vincentkslim/Ender-3/Ender-3 Mechanical/Ender-3 Parts/ASM Roller Z-Axis Left.SLDASM

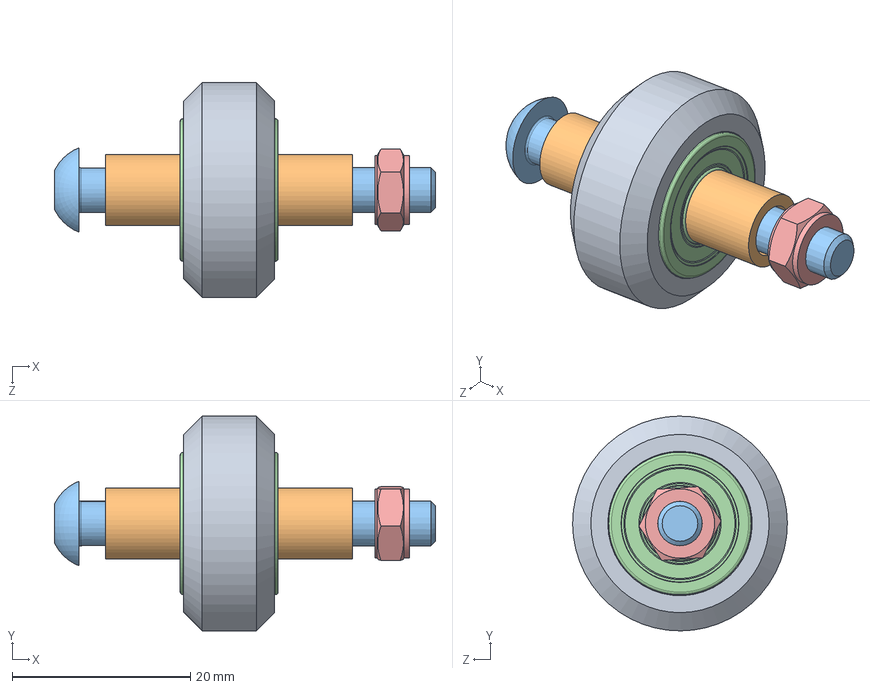
[picture p16: CAD file, 2020-07-11]
Ender-3 Mechanical/Ender-3 Parts/ASM Roller Z-Axis Left.SLDASM
42.8 x 24.1 x 24.1 mm
Rollers
Spacers for rollers x 2
M5X40 Pan Head Screw
625pillow x 2
M5 Self-locking nut
