vincentkslim/Ender-3/Ender-3 Mechanical/Ender-3 Parts/ASM Bed.SLDASM

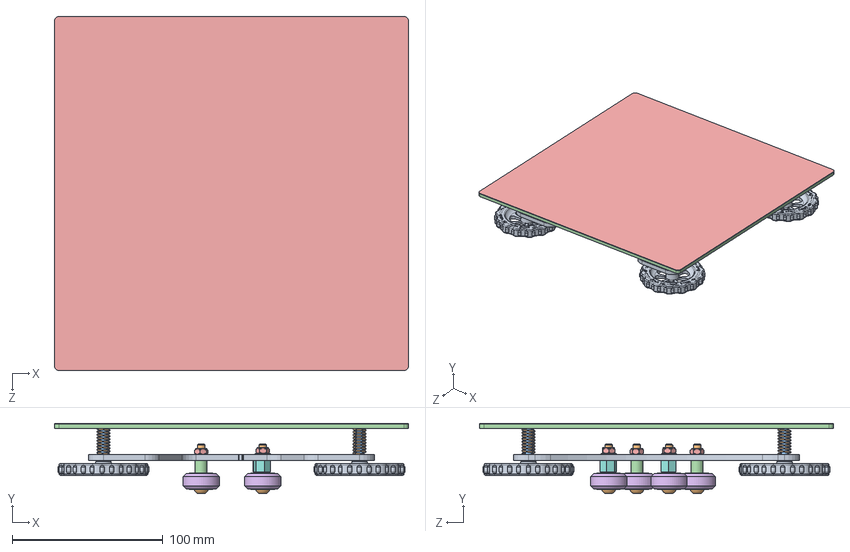
[picture p17: CAD file, 2020-07-11]
Ender-3 Mechanical/Ender-3 Parts/ASM Bed.SLDASM
235.0 x 46.7 x 235.0 mm
Y plate
M5X30 Pan Head Screw x 4
625pillow x 8
Spacers for rollers x 2
M5 Self-locking nut x 4
Rollers x 4
M5 washer x 2
Eccentric column x 2
Hand Twisted Nut x 4
Bed level springs x 4
M4X30 Flush Head Screw x 4
Hot bed
Hotbed_Surface
