vincentkslim/Ender-3/Ender-3 Mechanical/Ender-3 Parts/ASM Eccentrical Roller Z-Axis Right.SLDASM

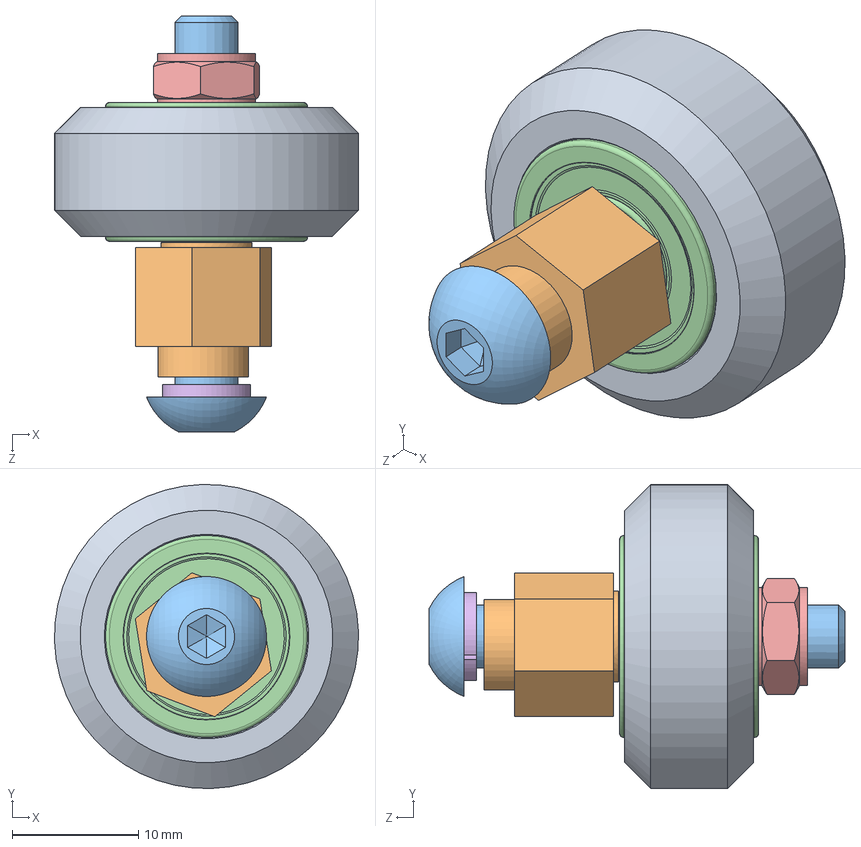
[picture p18: CAD file, 2020-07-11]
Ender-3 Mechanical/Ender-3 Parts/ASM Eccentrical Roller Z-Axis Right.SLDASM
24.1 x 24.1 x 33.0 mm
Rollers
Eccentric column
M5X30 Pan Head Screw
625pillow x 2
M5 Self-locking nut
M5 Split Washer
