vincentkslim/Ender-3/Ender-3 Mechanical/Ender-3 Parts/ASM Display.SLDASM

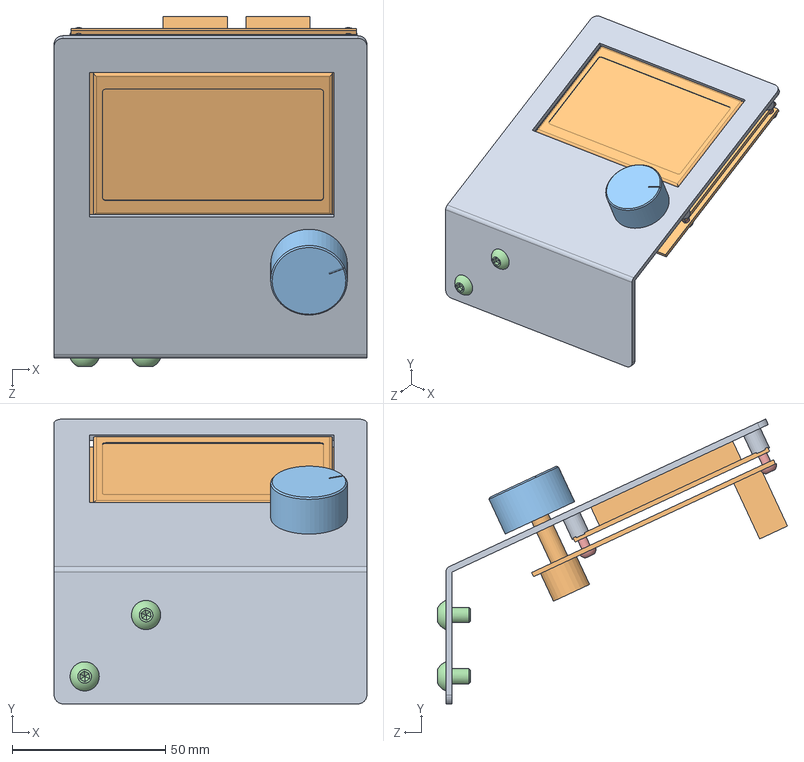
[picture p19: CAD file, 2020-04-29]
Ender-3 Mechanical/Ender-3 Parts/ASM Display.SLDASM
102.0 x 92.9 x 114.1 mm
LCD support
lcd
lcd Knob
M5X8Pan Head Screw x 2
M3X8 Pan Head Screw x 4
