vincentkslim/Ender-3/Ender-3 Mechanical/Ender-3 Parts/ASM Electronic Enclosure.SLDASM

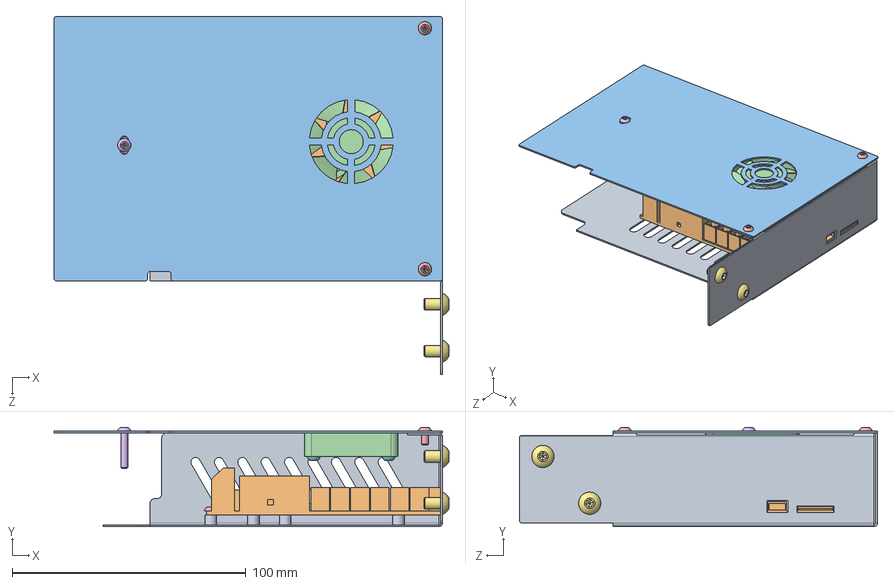
[picture p20: CAD file, 2020-04-29]
Ender-3 Mechanical/Ender-3 Parts/ASM Electronic Enclosure.SLDASM
168.8 x 42.5 x 153.0 mm
Sheetmetal enclosure bottom
Control panel
Sheetmetal enclosure top
Case fan
M3X6Pan Head Screw x 6
M3X16 Pan Head Screw
M5X8Pan Head Screw x 2
M3X10 Pan Head Screw x 2
