vincentkslim/Ender-3/Ender-3 Mechanical/Ender-3 Parts/ASM Y-Axis Limit Switch.SLDASM

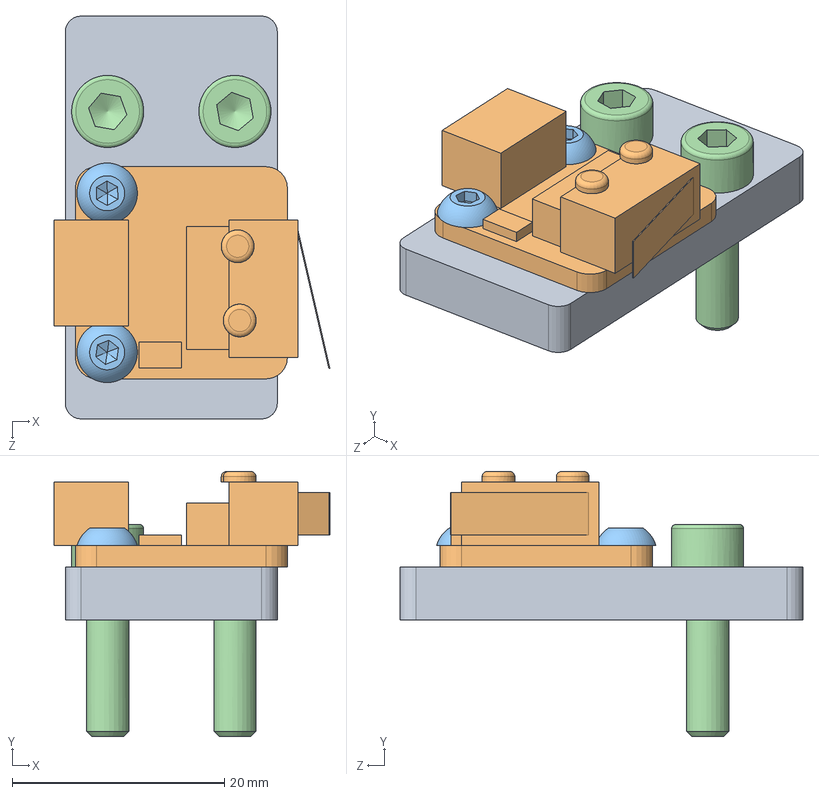
[picture p21: CAD file, 2020-04-29]
Ender-3 Mechanical/Ender-3 Parts/ASM Y-Axis Limit Switch.SLDASM
26.0 x 25.0 x 38.0 mm
Y limit switch bracket
limit switch
M3X6Pan Head Screw x 2
M4X16 Screw x 2
