vincentkslim/Ender-3/Ender-3 Mechanical/Ender-3 Parts/ASM Spool Holder.SLDASM

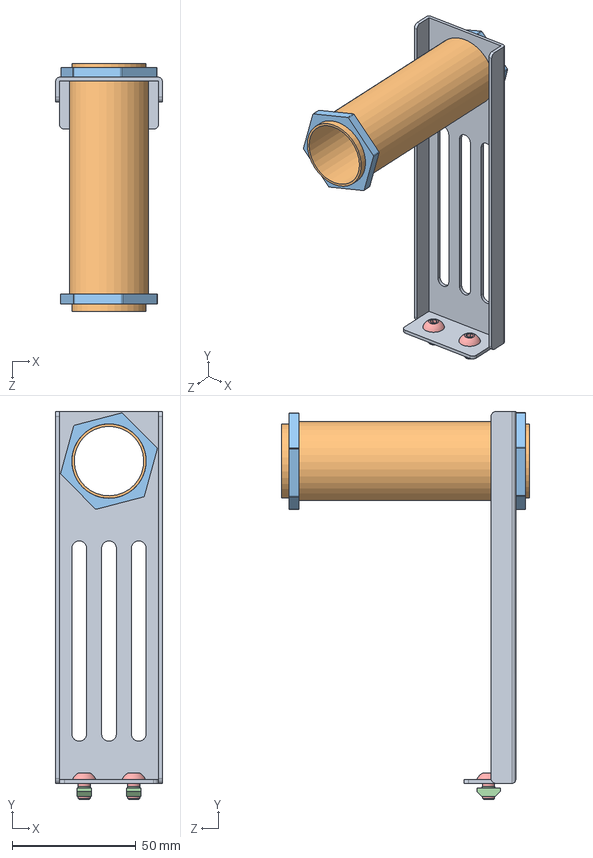
[picture p22: CAD file, 2020-04-29]
Ender-3 Mechanical/Ender-3 Parts/ASM Spool Holder.SLDASM
43.0 x 156.5 x 100.0 mm
Support frame
Support tube
M30 Plastic nut x 2
M4 T-Slot Nut x 2
M5X8Pan Head Screw x 2
