vincentkslim/Ender-3/Ender-3 Mechanical/Ender-3 Parts/ASM Y-Belt Tensioner.SLDASM

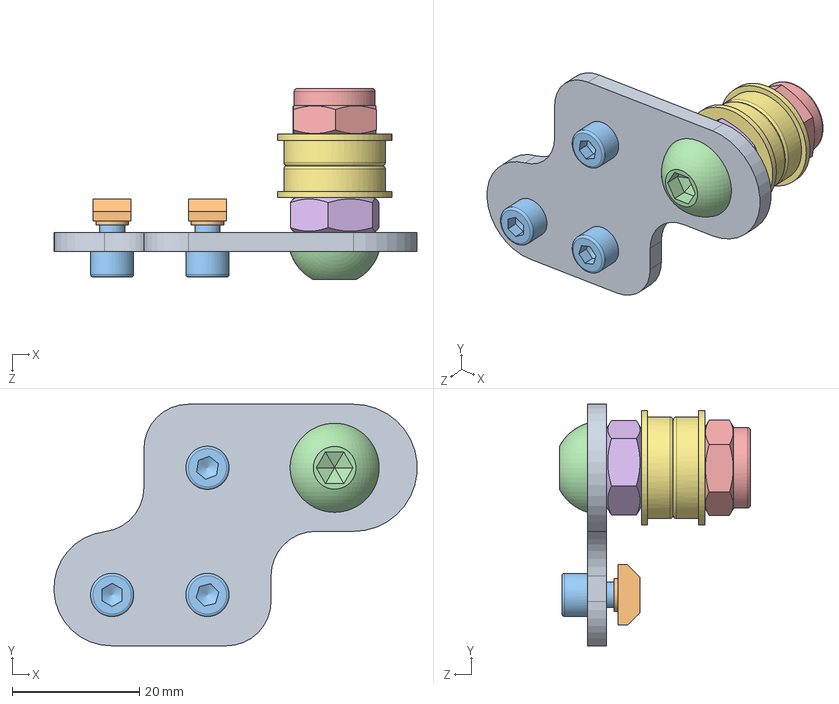
[picture p23: CAD file, 2020-04-29]
Ender-3 Mechanical/Ender-3 Parts/ASM Y-Belt Tensioner.SLDASM
57.1 x 38.0 x 30.1 mm
Y Adjustment Block
M4 T-Slot Nut x 3
M4X8 Socket Head Screw x 3
M8X25 Pan Head Screw
M8 Self-locking nut
M8 nut
F688 pillow x 2
