vincentkslim/Ender-3/Ender-3 Mechanical/Ender-3 Parts/ASM Z-Axis Limit Switch.SLDASM

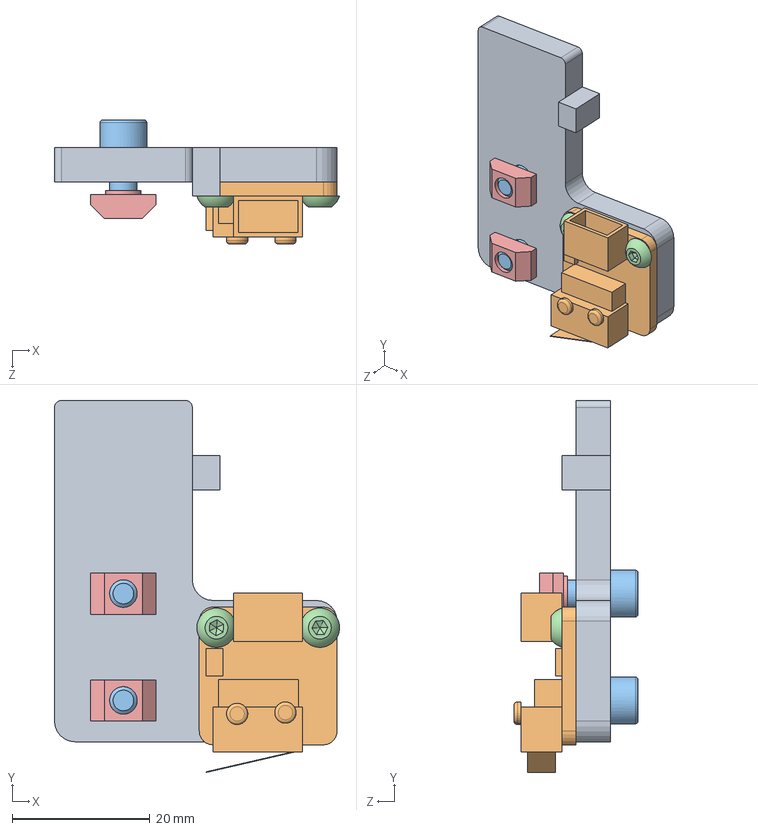
[picture p24: CAD file, 2020-04-29]
Ender-3 Mechanical/Ender-3 Parts/ASM Z-Axis Limit Switch.SLDASM
41.3 x 54.0 x 18.0 mm
Z limit switch bracket
limit switch
M4X10 Socket Head Screw x 2
M3X6Pan Head Screw x 2
M4 T-Slot Nut x 2
