vincentkslim/Ender-3/Ender-3 Mechanical/Ender-3 Parts/ASM Power Supply.SLDASM

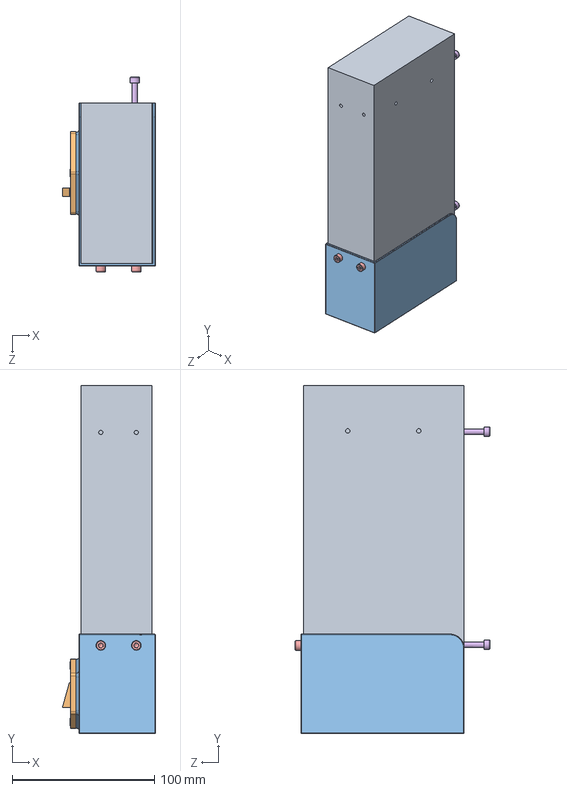
[picture p25: CAD file, 2020-04-29]
Ender-3 Mechanical/Ender-3 Parts/ASM Power Supply.SLDASM
65.5 x 245.0 x 137.0 mm
24V15A power supply
power switch
Power holder
M3X10 Flush Head Screw x 2
M4X8 Socket Head Screw x 2
M4X20 Socket Head Screw x 2
