vincentkslim/Ender-3/Ender-3 Mechanical/Ender-3 Parts/ASM Z-Axis.SLDASM

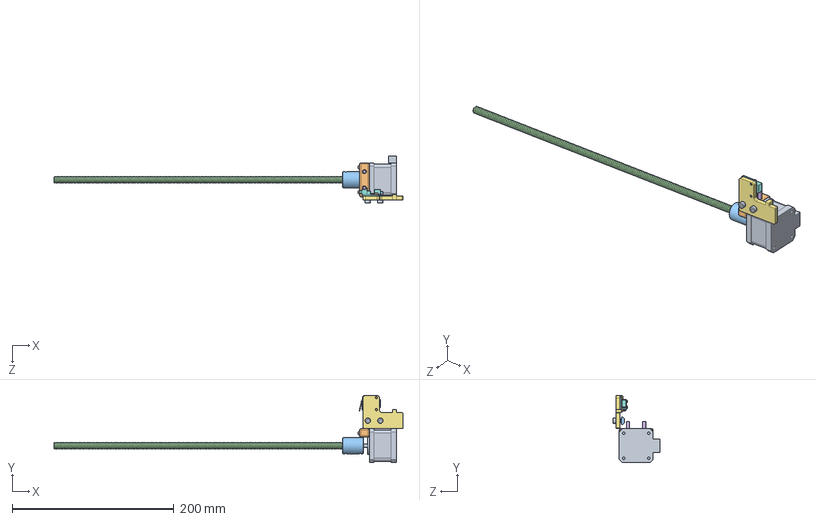
[picture p26: CAD file, 2020-04-29]
Ender-3 Mechanical/Ender-3 Parts/ASM Z-Axis.SLDASM
431.8 x 83.3 x 58.7 mm
42-34 motor
Z motor bracket
Z coupler
Z threaded rod
M3X16 Pan Head Screw x 2
M4X18 Flush Head Screw x 2
Z limit switch bracket
limit switch
M4X10 Socket Head Screw x 2
M3X6Pan Head Screw x 2
M4 T-Slot Nut x 2
