vincentkslim/Ender-3/Ender-3 Mechanical/Ender-3 Parts/ASM Frame.SLDASM

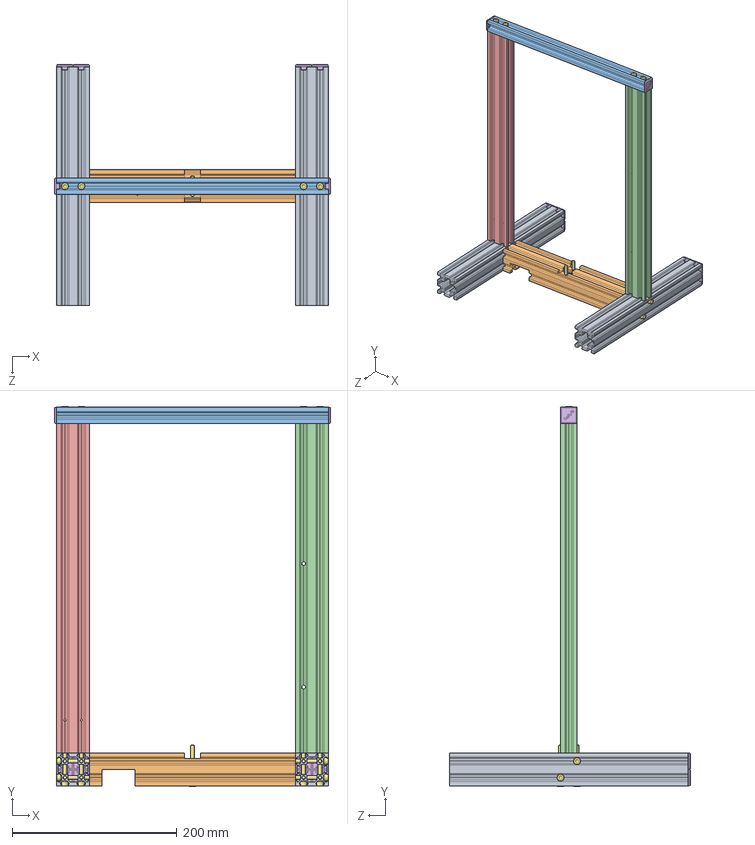
[picture p27: CAD file, 2020-04-09]
Ender-3 Mechanical/Ender-3 Parts/ASM Frame.SLDASM
335.7 x 461.6 x 292.9 mm
4040 profile x 2
4040-3 profile
2020-2 profile
2040-3R profile
2040-3L profile
2020 Endcap x 10
M5X45 Socket Head Screw x 14
