vincentkslim/Ender-3/Ender-3 Mechanical/Ender-3 Parts/ASM Y-Axis.SLDASM

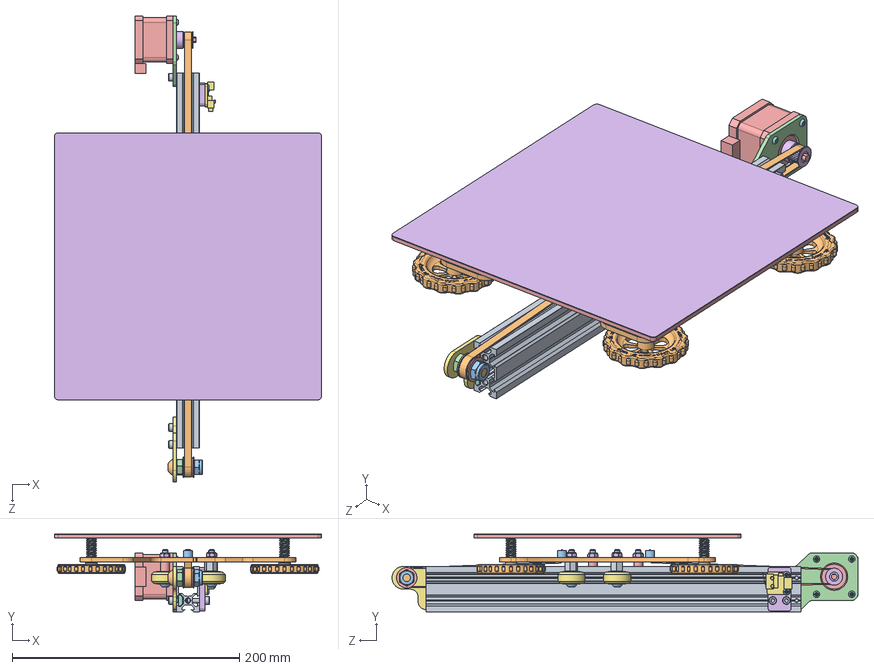
[picture p28: CAD file, 2020-04-09]
Ender-3 Mechanical/Ender-3 Parts/ASM Y-Axis.SLDASM
235.0 x 68.5 x 410.1 mm
2040-2 profile
Y belt
Copper cover x 2
Y Motor holder
42-34 motor
2GT-pulley
Y Adjustment Block
M4 T-Slot Nut x 3
M4X8 Socket Head Screw x 3
M8X25 Pan Head Screw
M8 Self-locking nut
M8 nut
F688 pillow x 2
Y limit switch bracket
limit switch
M3X6Pan Head Screw x 6
M4X16 Screw x 4
Y plate
M5X30 Pan Head Screw x 4
625pillow x 8
Spacers for rollers x 2
M5 Self-locking nut x 4
Rollers x 4
M5 washer x 2
Eccentric column x 2
Hand Twisted Nut x 4
Bed level springs x 4
M4X30 Flush Head Screw x 4
Hot bed
Hotbed_Surface
