vincentkslim/Ender-3/Ender-3 Mechanical/Ender-3 Upgrades/raspberry-pi-3-model-b-reference-design-solidworks-cad-rpi-raspberrypi-raspberry-pi-1.snapshot.83/Solidworks Complete Assembly/Rpi components/RPi3_ModelB v1.sldasm

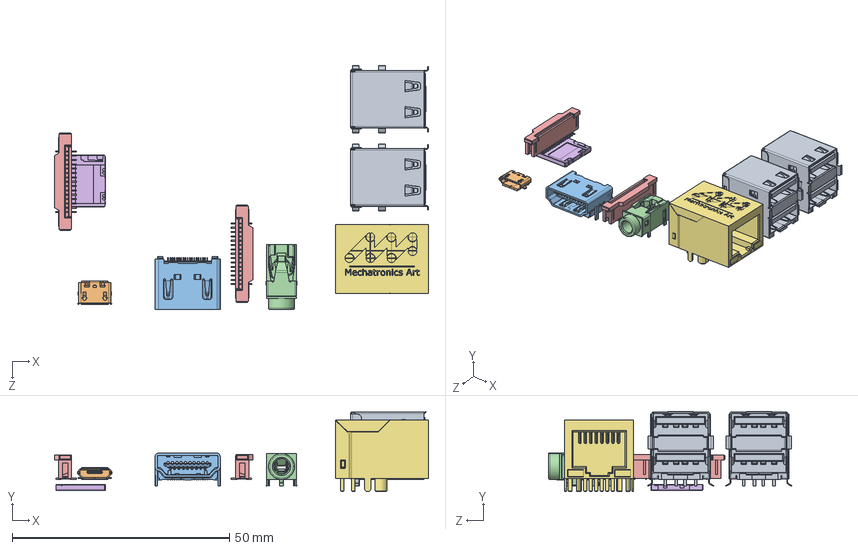
[picture p29: CAD file, 2020-04-29]
Ender-3 Mechanical/Ender-3 Upgrades/raspberry-pi-3-model-b-reference-design-solidworks-cad-rpi-raspberrypi-raspberry-pi-1.snapshot.83/Solidworks Complete Assembly/Rpi components/RPi3_ModelB v1.sldasm
86.1 x 18.5 x 56.1 mm
MOLEX_672983090 x 2
molex_0473460001
molex_0471510001
PJ-322
te_1-1734248-5 x 2
MOLEX_1040310811
raspberry_pi_B_(RJ45)
