vincentkslim/Ender-3/Ender-3 Mechanical/Ender-3 Upgrades/ABL/4mm allen key.SLDPRT

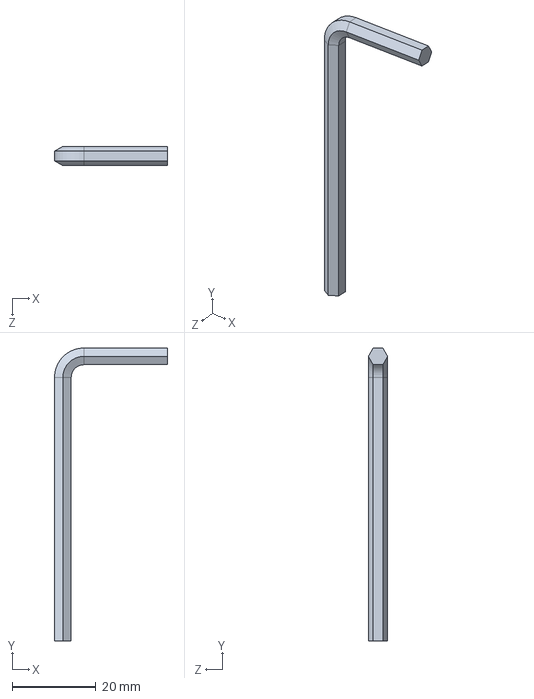
[picture p30: CAD file, 2020-04-29]
Ender-3 Mechanical/Ender-3 Upgrades/ABL/4mm allen key.SLDPRT
27.0 x 70.0 x 4.62 mm
