vincentkslim/Ender-3/Ender-3 Mechanical/Ender-3 Upgrades/Direct Drive/_stl/direct_drive_fits_e3d_v6_hero_me.STL

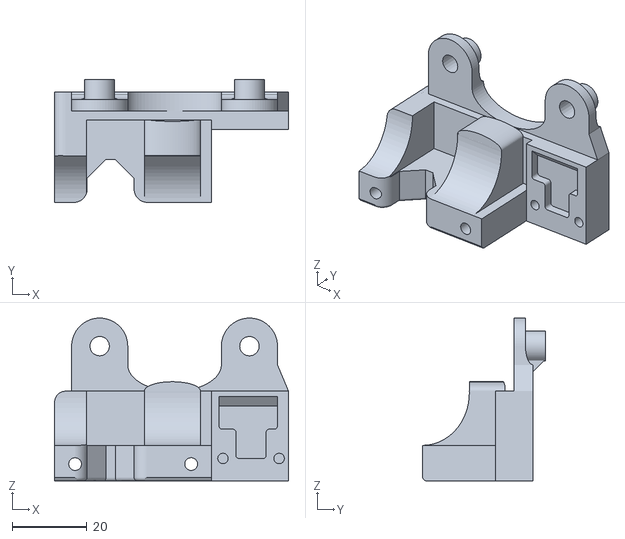
[picture p31: CAD file, 2020-04-29]
Ender-3 Mechanical/Ender-3 Upgrades/Direct Drive/_stl/direct_drive_fits_e3d_v6_hero_me.STL
62.5 x 32.8 x 43.5
