vincentkslim/Ender-3/Ender-3 Mechanical/Ender-3 Upgrades/Direct Drive/_test/part2.sldprt

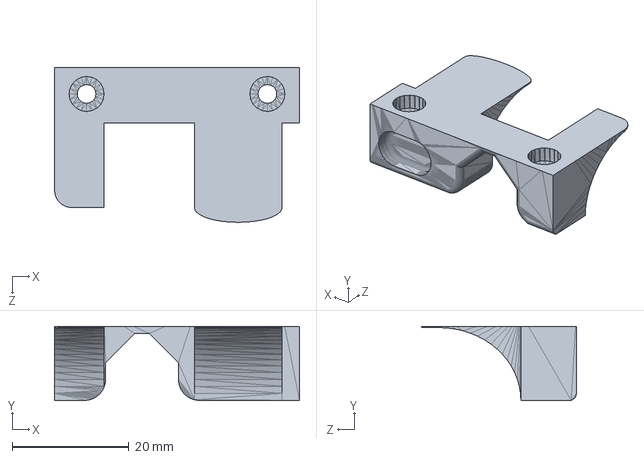
[picture p32: CAD file, 2020-04-29]
Ender-3 Mechanical/Ender-3 Upgrades/Direct Drive/_test/part2.sldprt
42.0 x 12.7 x 26.5 mm
