vincentkslim/Ender-3/Ender-3 Mechanical/Ender-3 Upgrades/Hero Me E3D V6 Mount/_stl/Hero_Me_E3D_Base_2_Gen2.stl

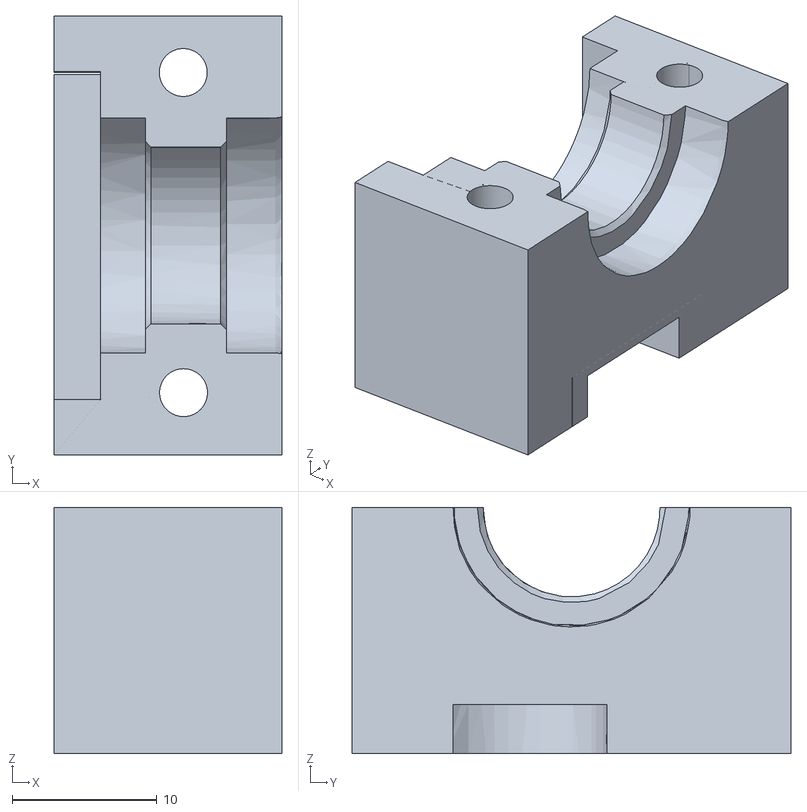
[picture p33: CAD file, 2020-04-29]
Ender-3 Mechanical/Ender-3 Upgrades/Hero Me E3D V6 Mount/_stl/Hero_Me_E3D_Base_2_Gen2.stl
15.7 x 30.3 x 17.0
