vincentkslim/Ender-3/Ender-3 Mechanical/Ender-3 Upgrades/Hero Me E3D V6 Mount/_test/1.5mm allen key test 2.2.STL

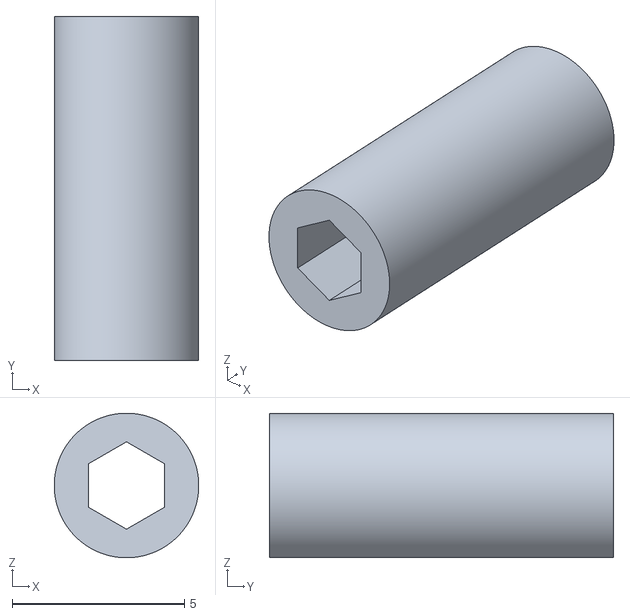
[picture p34: CAD file, 2020-04-29]
Ender-3 Mechanical/Ender-3 Upgrades/Hero Me E3D V6 Mount/_test/1.5mm allen key test 2.2.STL
4.20 x 10.0 x 4.20
