vincentkslim/Ender-3/Ender-3 Mechanical/Ender-3 Upgrades/Hero Me E3D V6 Mount/Hero_Me_Base_Lock_Gen3.SLDPRT

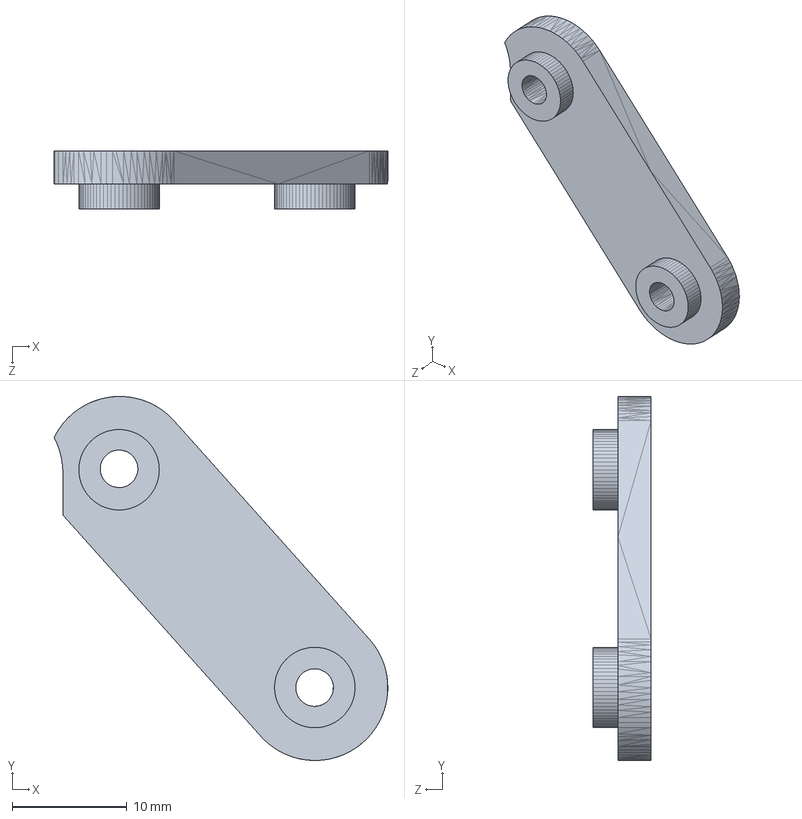
[picture p35: CAD file, 2020-04-29]
Ender-3 Mechanical/Ender-3 Upgrades/Hero Me E3D V6 Mount/Hero_Me_Base_Lock_Gen3.SLDPRT
29.0 x 31.7 x 5.07 mm
