vincentkslim/Ender-3/Ender-3 Mechanical/Ender-3 Upgrades/Radial Cooling Fan 50mm DC12V/Radial-Cooling-Fan-5015-DC12V.STEP

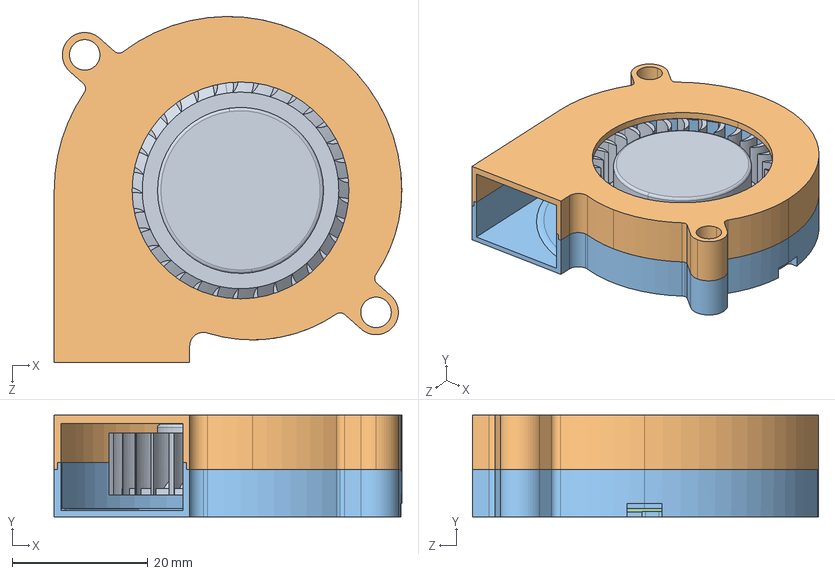
[picture p36: CAD file, 2020-07-11]
Ender-3 Mechanical/Ender-3 Upgrades/Radial Cooling Fan 50mm DC12V/Radial-Cooling-Fan-5015-DC12V.STEP
51.3 x 15.0 x 51.1 mm
turbine
top
bottom
