vincentkslim/Ender-3/Ender-3 Mechanical/Ender-3 Upgrades/Rear Electronics Case/_stl/fan_grill_3mm.STL

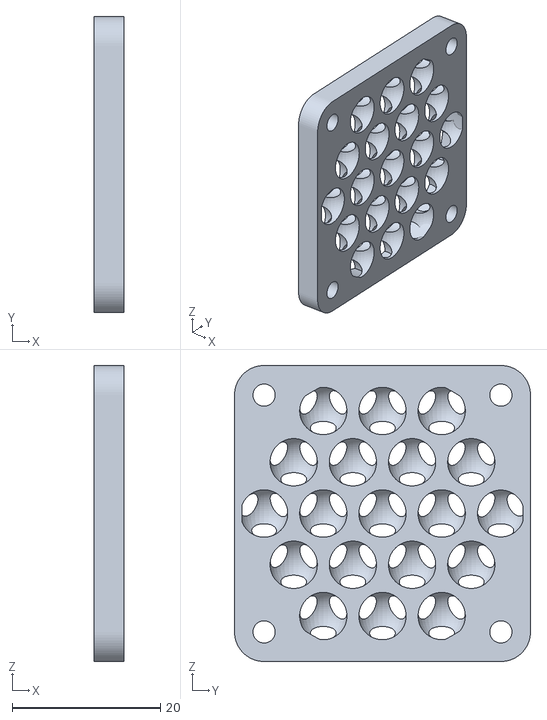
[picture p37: CAD file, 2020-04-29]
Ender-3 Mechanical/Ender-3 Upgrades/Rear Electronics Case/_stl/fan_grill_3mm.STL
4.00 x 40.0 x 40.0
