vincentkslim/Ender-3/Ender-3 Mechanical/Ender-3 Upgrades/Rear Electronics Case/case_right.SLDPRT

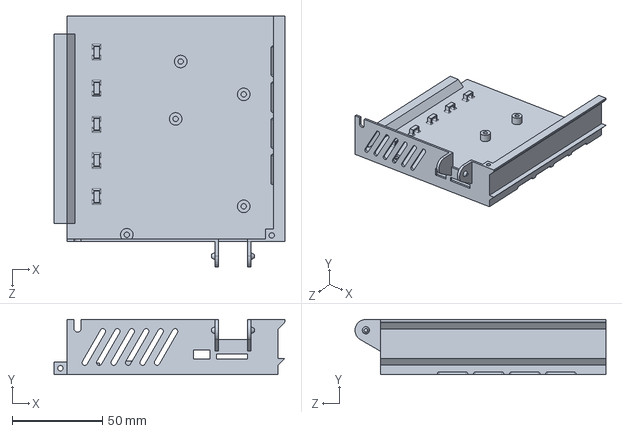
[picture p38: CAD file, 2020-12-05]
Ender-3 Mechanical/Ender-3 Upgrades/Rear Electronics Case/case_right.SLDPRT
127.8 x 30.5 x 139.0 mm
