vincentkslim/Ender-3/Ender-3 Mechanical/Ender-3 Upgrades/Samla Box clips/001.SLDPRT

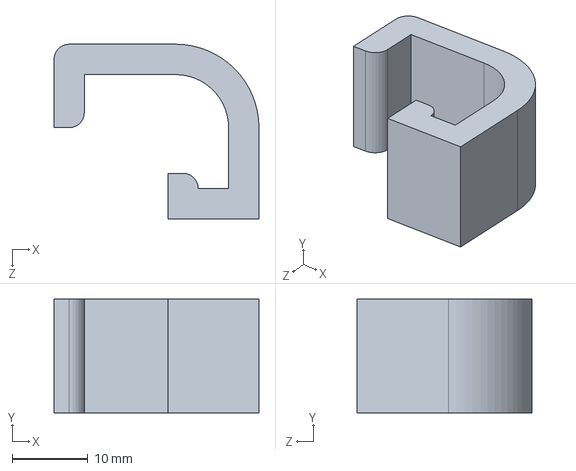
[picture p39: CAD file, 2020-12-05]
Ender-3 Mechanical/Ender-3 Upgrades/Samla Box clips/001.SLDPRT
27.0 x 15.0 x 23.0 mm
