vincentkslim/Ender-3/Ender-3 Mechanical/Ender-3 Upgrades/X Carriage/M6 thread test.SLDPRT

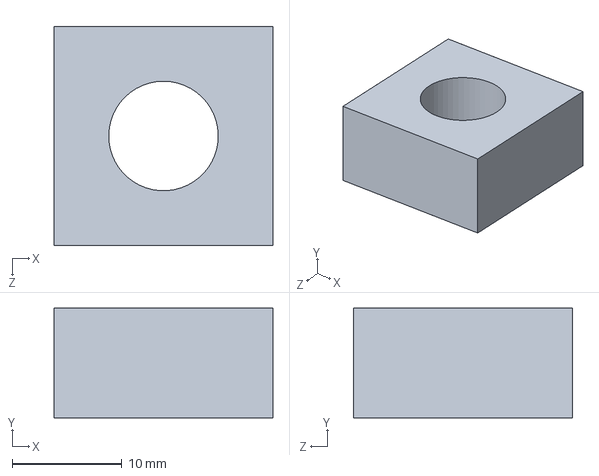
[picture p40: CAD file, 2020-12-05]
Ender-3 Mechanical/Ender-3 Upgrades/X Carriage/M6 thread test.SLDPRT
20.0 x 10.0 x 20.0 mm
