vincentkslim/Ender-3/Ender-3 Mechanical/Ender-3 Upgrades/ABL/1.5mm allen key.SLDPRT

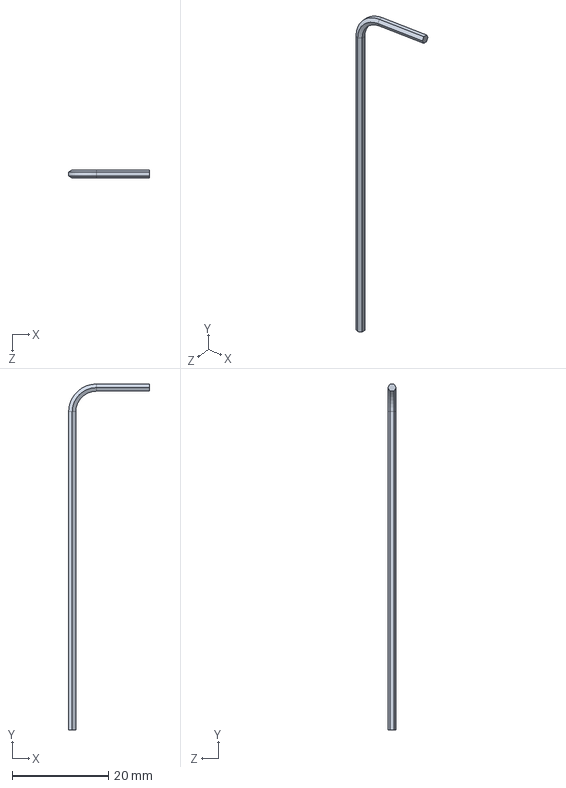
[picture p41: CAD file, 2020-04-29]
Ender-3 Mechanical/Ender-3 Upgrades/ABL/1.5mm allen key.SLDPRT
16.8 x 71.8 x 1.73 mm
