vincentkslim/Ender-3/Ender-3 Mechanical/Ender-3 Upgrades/Direct Drive/_test/Adapter_for_Red_Metal_Extruder_E3D_V6.STL

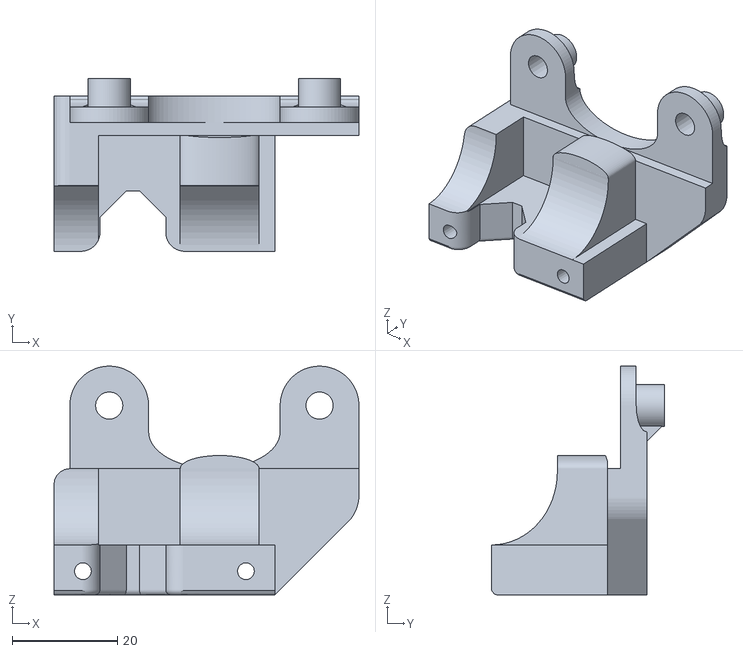
[picture p42: CAD file, 2020-04-29]
Ender-3 Mechanical/Ender-3 Upgrades/Direct Drive/_test/Adapter_for_Red_Metal_Extruder_E3D_V6.STL
58.0 x 32.8 x 43.5
