vincentkslim/Ender-3/Ender-3 Mechanical/Ender-3 Upgrades/Direct Drive/_test/fits_hero_me/Body3.sldprt

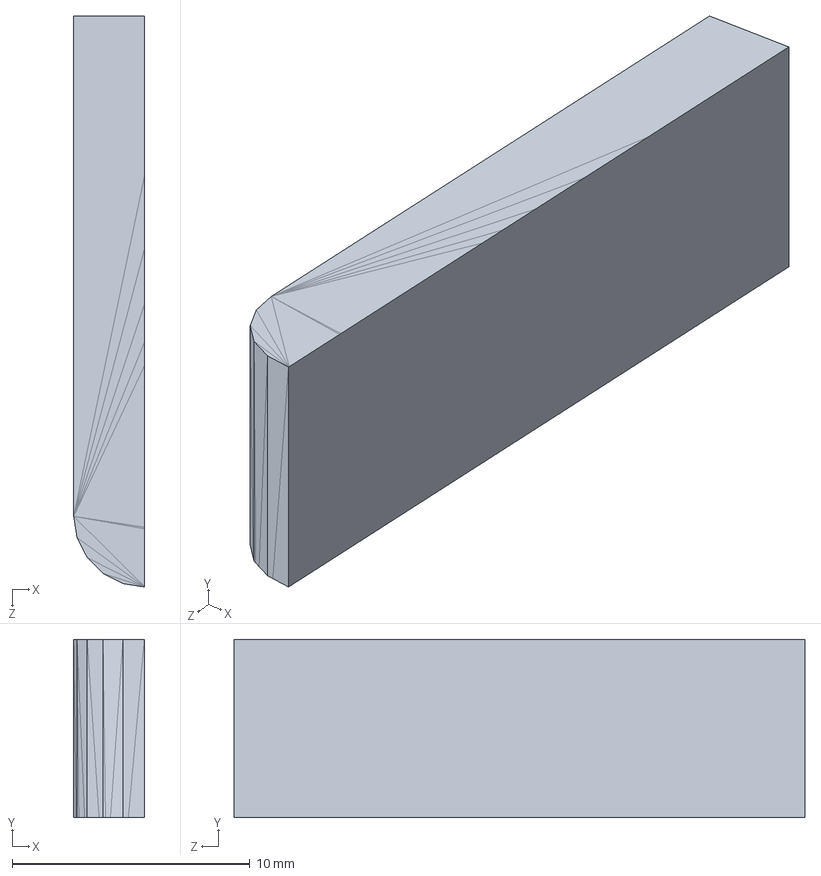
[picture p43: CAD file, 2020-04-29]
Ender-3 Mechanical/Ender-3 Upgrades/Direct Drive/_test/fits_hero_me/Body3.sldprt
2.97 x 7.50 x 24.0 mm
