vincentkslim/Ender-3/Ender-3 Mechanical/Ender-3 Upgrades/Hero Me E3D V6 Mount/_stl/Hero_Me_E3D_Base_1_Gen2c.stl

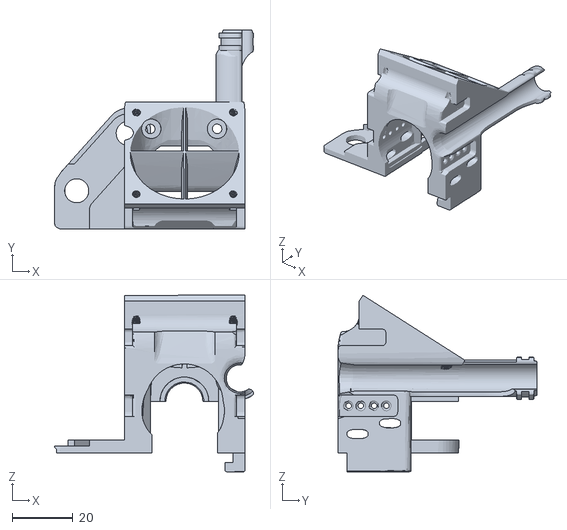
[picture p44: CAD file, 2020-04-29]
Ender-3 Mechanical/Ender-3 Upgrades/Hero Me E3D V6 Mount/_stl/Hero_Me_E3D_Base_1_Gen2c.stl
65.8 x 65.9 x 58.4
