vincentkslim/Ender-3/Ender-3 Mechanical/Ender-3 Upgrades/Hero Me E3D V6 Mount/_test/1.5mm allen key test 2.1.STL

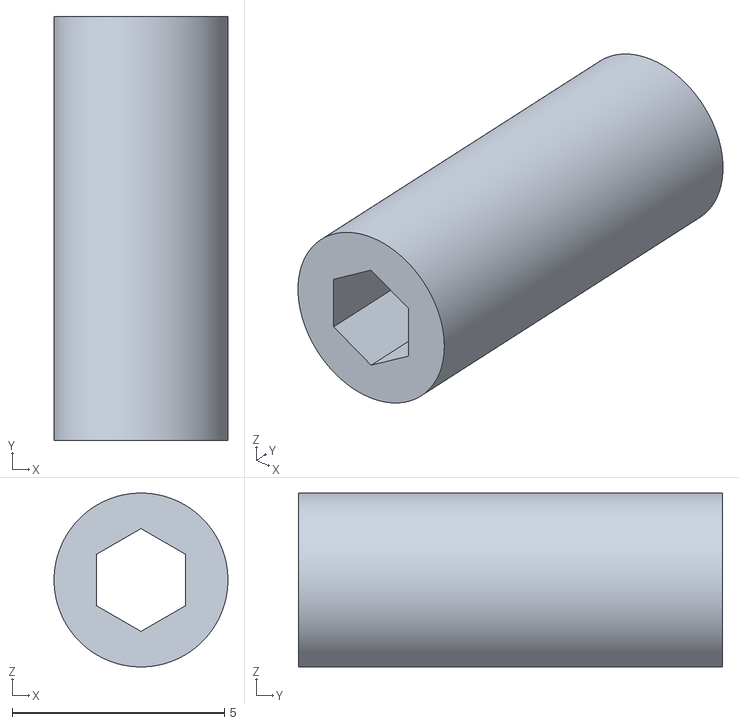
[picture p45: CAD file, 2020-04-29]
Ender-3 Mechanical/Ender-3 Upgrades/Hero Me E3D V6 Mount/_test/1.5mm allen key test 2.1.STL
4.10 x 10.0 x 4.10
