vincentkslim/Ender-3/Ender-3 Mechanical/Ender-3 Upgrades/Hero Me E3D V6 Mount/Hero Me Base Lock Allen Key Mount.SLDPRT

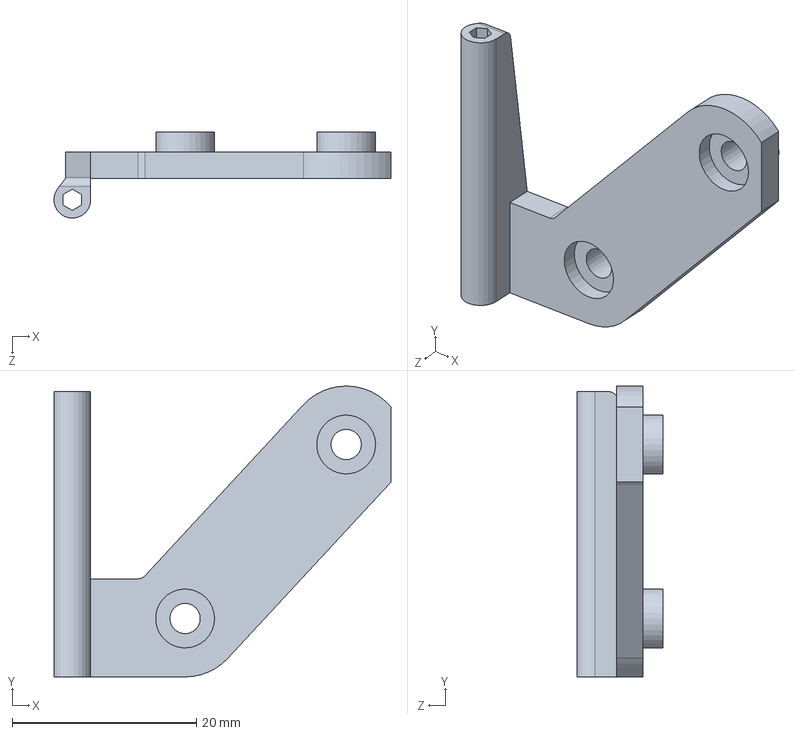
[picture p46: CAD file, 2020-04-29]
Ender-3 Mechanical/Ender-3 Upgrades/Hero Me E3D V6 Mount/Hero Me Base Lock Allen Key Mount.SLDPRT
36.6 x 31.6 x 9.38 mm
