vincentkslim/Ender-3/Ender-3 Mechanical/Ender-3 Upgrades/Radial Cooling Fan 50mm DC12V/top.SLDPRT

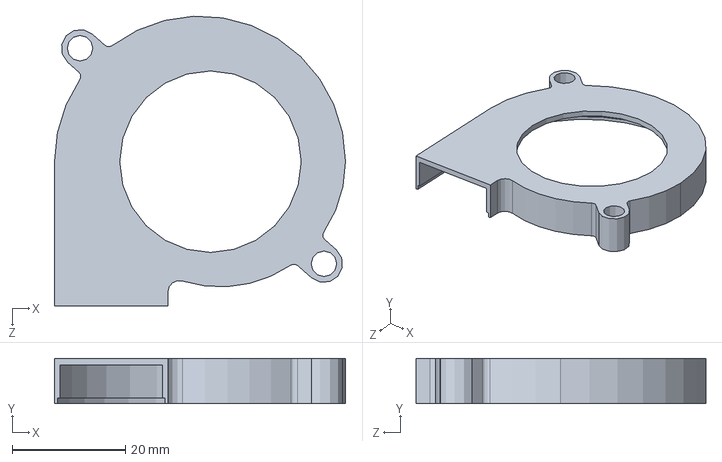
[picture p47: CAD file, 2020-07-11]
Ender-3 Mechanical/Ender-3 Upgrades/Radial Cooling Fan 50mm DC12V/top.SLDPRT
51.3 x 8.00 x 51.0 mm
