vincentkslim/Ender-3/Ender-3 Mechanical/Ender-3 Upgrades/Rear Electronics Case/_stl/rpi_hole_position.STL

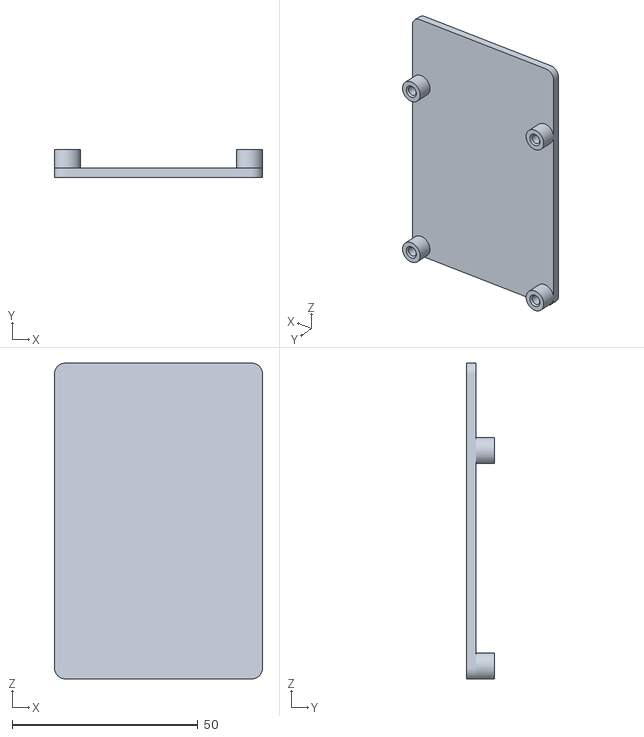
[picture p48: CAD file, 2020-04-09]
Ender-3 Mechanical/Ender-3 Upgrades/Rear Electronics Case/_stl/rpi_hole_position.STL
56.0 x 7.50 x 85.0
