vincentkslim/Ender-3/Ender-3 Mechanical/Ender-3 Upgrades/Rear Electronics Case/_test/LM2596S_hole_position.SLDPRT

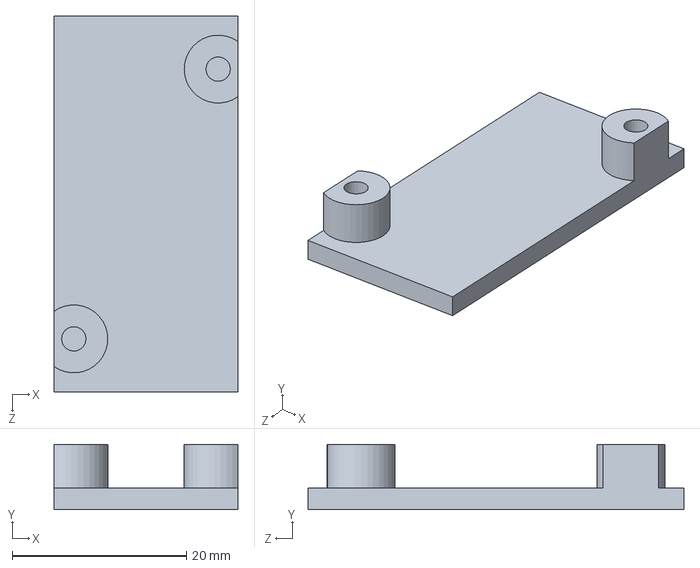
[picture p49: CAD file, 2020-04-09]
Ender-3 Mechanical/Ender-3 Upgrades/Rear Electronics Case/_test/LM2596S_hole_position.SLDPRT
21.1 x 7.50 x 43.2 mm
