vincentkslim/Ender-3/Ender-3 Mechanical/Ender-3 Upgrades/X Carriage/_stl/M4 thread test.STL

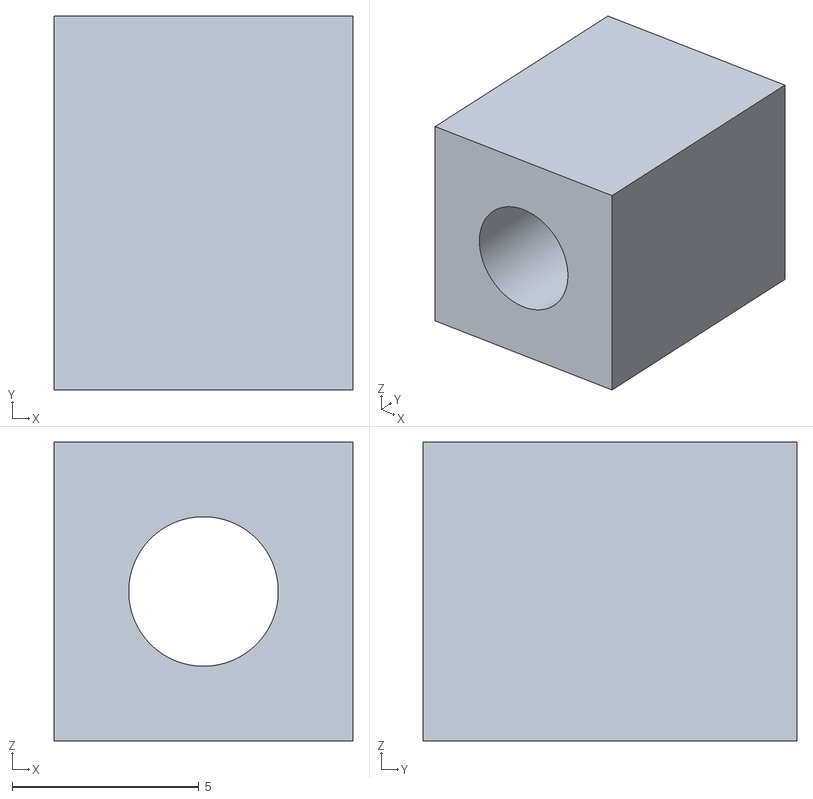
[picture p50: CAD file, 2020-12-05]
Ender-3 Mechanical/Ender-3 Upgrades/X Carriage/_stl/M4 thread test.STL
8.00 x 10.0 x 8.00
