vincentkslim/Ender-3/Ender-3 Mechanical/Ender-3 Parts/M6 Pneumatic joint.SLDPRT

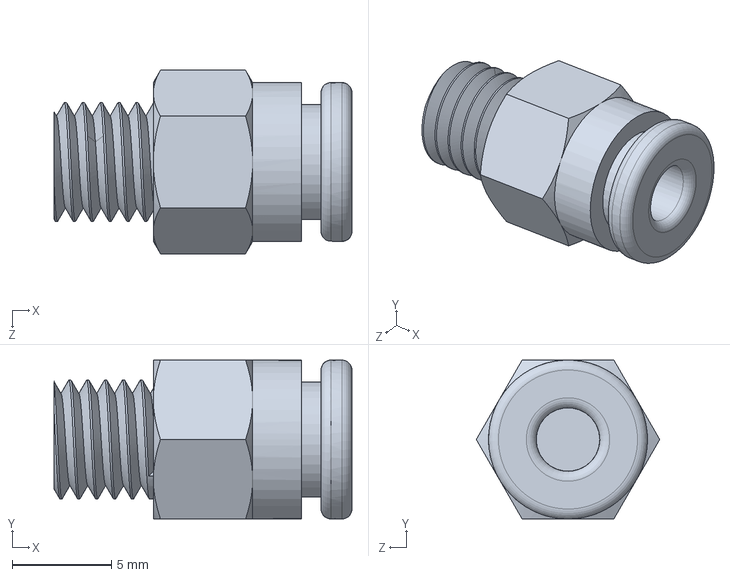
[picture p51: CAD file, 2020-12-05]
Ender-3 Mechanical/Ender-3 Parts/M6 Pneumatic joint.SLDPRT
15.0 x 8.00 x 9.24 mm
