vincentkslim/Ender-3/Ender-3 Mechanical/Ender-3 Upgrades/Direct Drive/_test/Adapter_for_Red_Metal_Extruder.SLDPRT

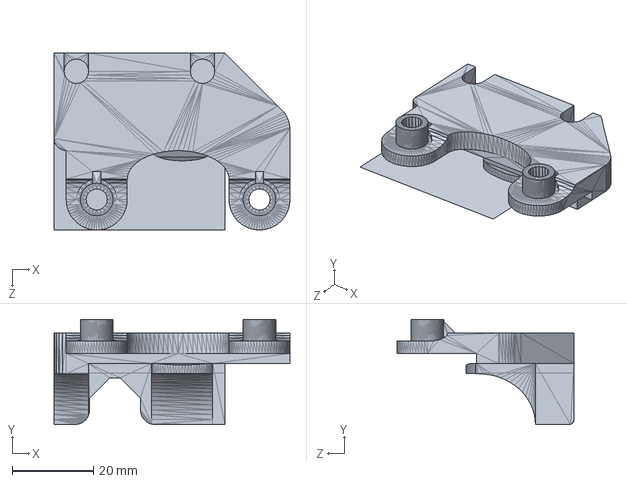
[picture p52: CAD file, 2020-04-29]
Ender-3 Mechanical/Ender-3 Upgrades/Direct Drive/_test/Adapter_for_Red_Metal_Extruder.SLDPRT
58.0 x 25.8 x 43.5 mm
