vincentkslim/Ender-3/Ender-3 Mechanical/Ender-3 Upgrades/Direct Drive/_test/fits_hero_me/Body2.sldprt

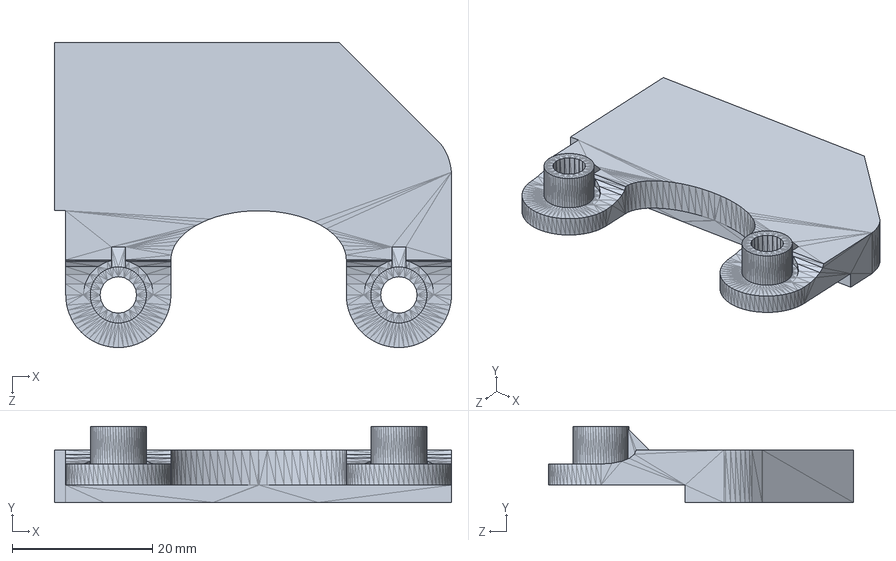
[picture p53: CAD file, 2020-04-29]
Ender-3 Mechanical/Ender-3 Upgrades/Direct Drive/_test/fits_hero_me/Body2.sldprt
56.6 x 10.9 x 43.5 mm
