vincentkslim/Ender-3/Ender-3 Mechanical/Ender-3 Upgrades/Hero Me E3D V6 Mount/_stl/Hero_Me_OEM_4010_duct_Gen2f.stl

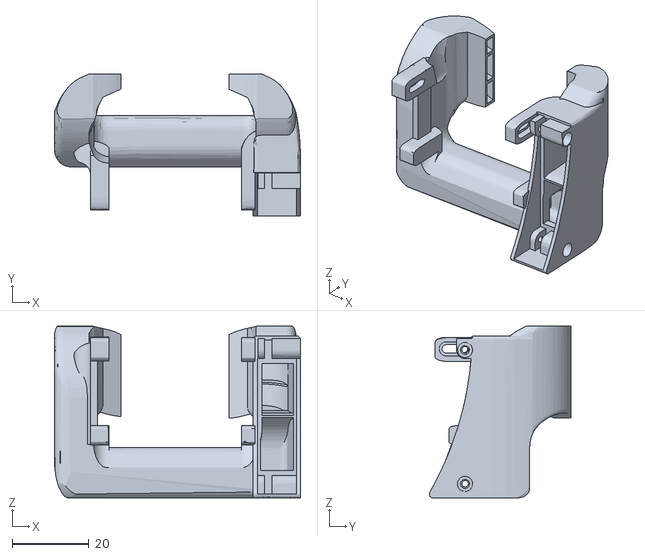
[picture p54: CAD file, 2020-04-29]
Ender-3 Mechanical/Ender-3 Upgrades/Hero Me E3D V6 Mount/_stl/Hero_Me_OEM_4010_duct_Gen2f.stl
64.3 x 37.0 x 44.9
