vincentkslim/Ender-3/Ender-3 Mechanical/Ender-3 Upgrades/Radial Cooling Fan 50mm DC12V/bottom.SLDPRT

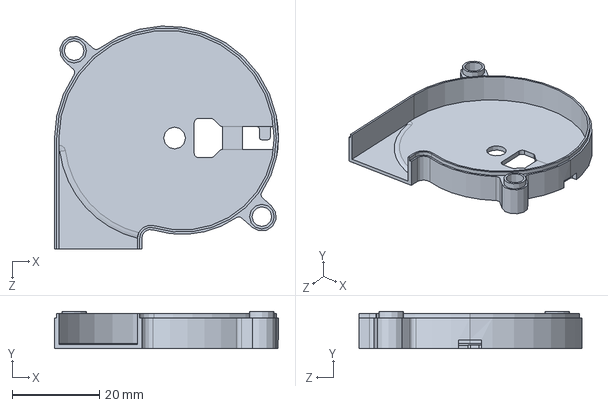
[picture p55: CAD file, 2020-07-11]
Ender-3 Mechanical/Ender-3 Upgrades/Radial Cooling Fan 50mm DC12V/bottom.SLDPRT
51.3 x 8.50 x 51.0 mm
