vincentkslim/Ender-3/Ender-3 Mechanical/Ender-3 Upgrades/raspberry-pi-3-model-b-reference-design-solidworks-cad-rpi-raspberrypi-raspberry-pi-1.snapshot.83/Solidworks Complete Assembly/Rpi components/Raspberry Pi 349.sldprt

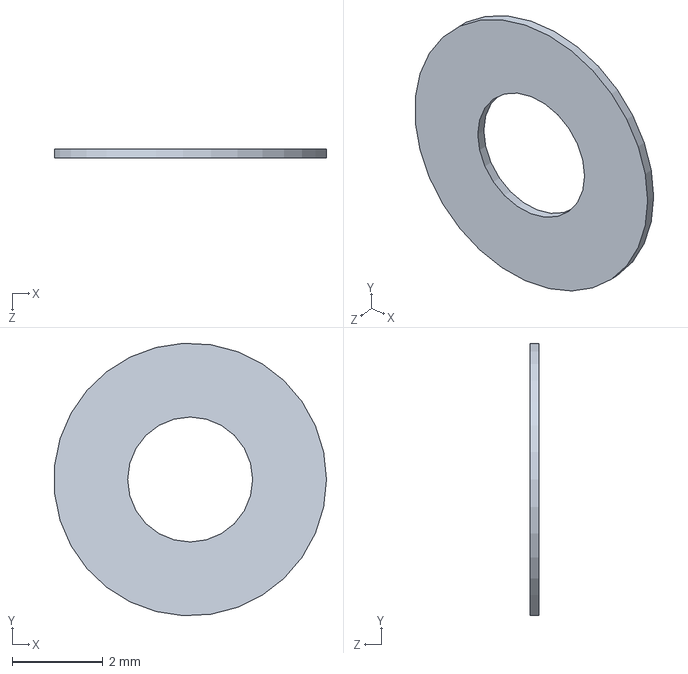
[picture p56: CAD file, 2020-07-11]
Ender-3 Mechanical/Ender-3 Upgrades/raspberry-pi-3-model-b-reference-design-solidworks-cad-rpi-raspberrypi-raspberry-pi-1.snapshot.83/Solidworks Complete Assembly/Rpi components/Raspberry Pi 349.sldp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
5.98 x 5.99 x 0.2 mm
