vincentkslim/Ender-3/Ender-3 Mechanical/Ender-3 Upgrades/Rear Electronics Case/_test/motherboad_hole_position.SLDPRT

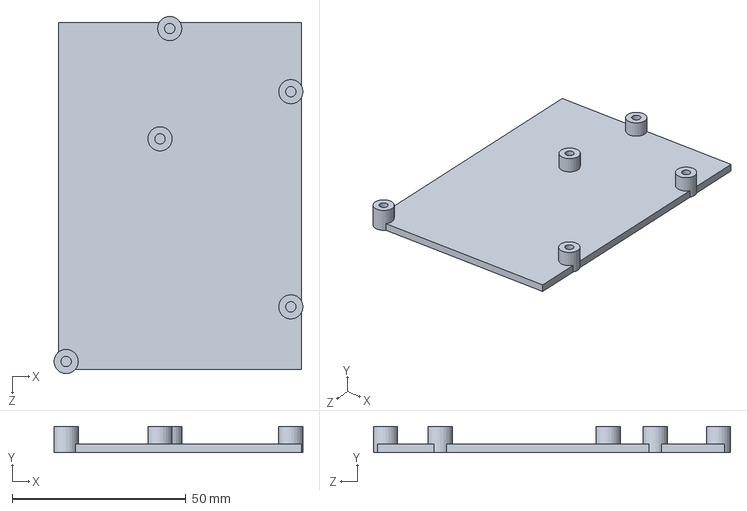
[picture p57: CAD file, 2020-04-09]
Ender-3 Mechanical/Ender-3 Upgrades/Rear Electronics Case/_test/motherboad_hole_position.SLDPRT
71.8 x 7.50 x 103.0 mm
