vincentkslim/Ender-3/Ender-3 Mechanical/Ender-3 Upgrades/X Carriage/003.SLDPRT

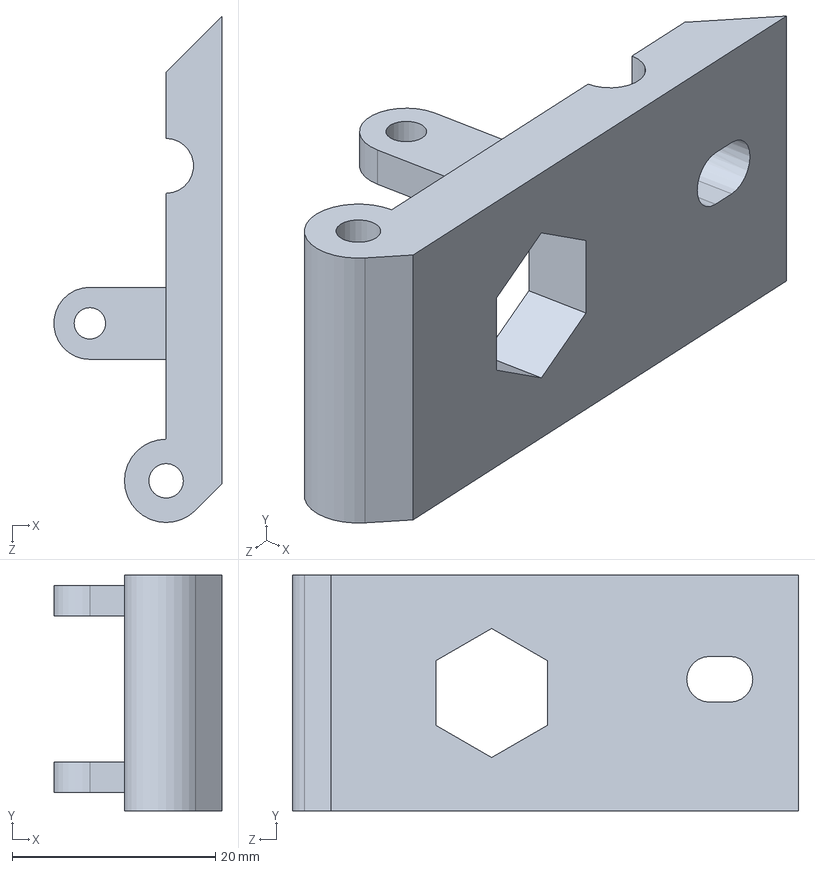
[picture p58: CAD file, 2020-12-05]
Ender-3 Mechanical/Ender-3 Upgrades/X Carriage/003.SLDPRT
16.5 x 23.2 x 49.8 mm
