vincentkslim/Ender-3/Ender-3 Mechanical/Ender-3 Upgrades/X Carriage/_stl/ptfe tube test.STL

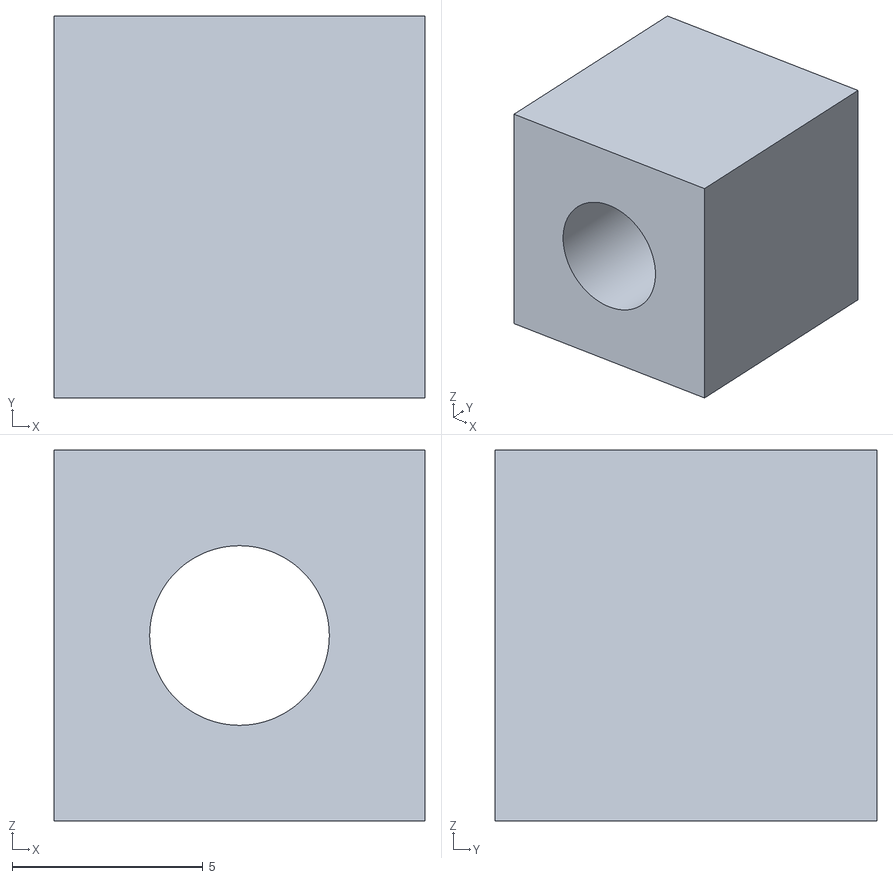
[picture p59: CAD file, 2020-12-05]
Ender-3 Mechanical/Ender-3 Upgrades/X Carriage/_stl/ptfe tube test.STL
9.70 x 10.0 x 9.70
