vincentkslim/Ender-3/Ender-3 Mechanical/Ender-3 Parts/E idler tensioner.SLDPRT

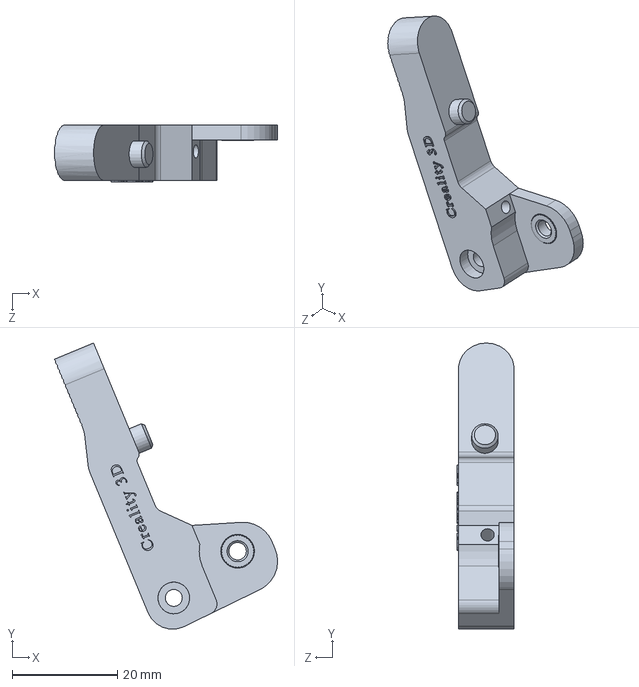
[picture p60: CAD file, 2020-12-05]
Ender-3 Mechanical/Ender-3 Parts/E idler tensioner.SLDPRT
42.4 x 54.2 x 10.9 mm
