vincentkslim/Ender-3/Ender-3 Mechanical/Ender-3 Upgrades/Direct Drive/_test/fits_hero_me/direct_drive_fits_e3d_v6_hero_me_M3x30.STL

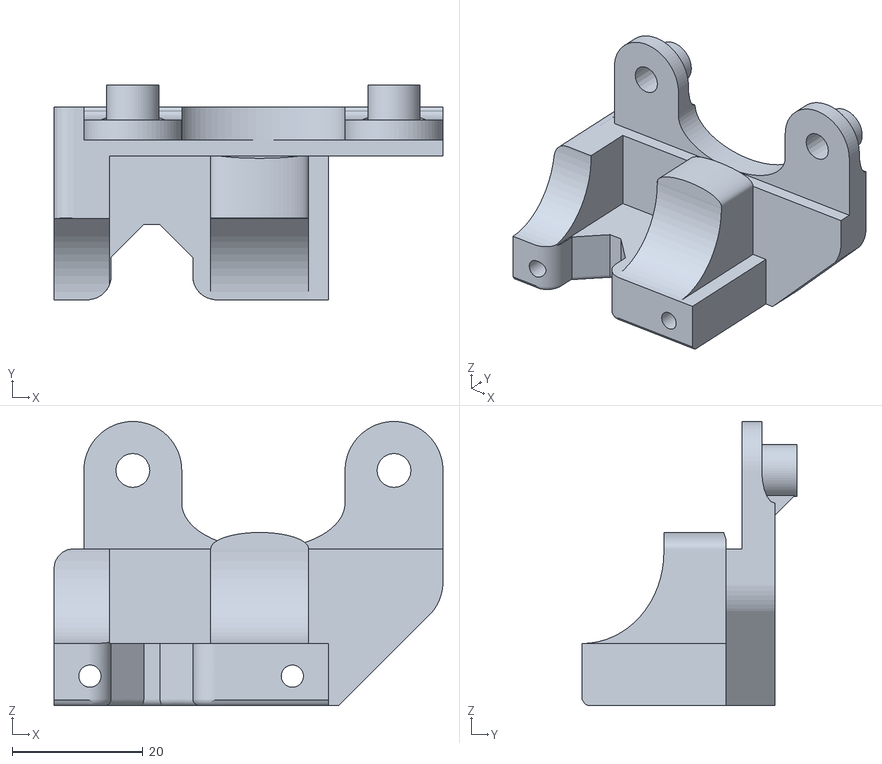
[picture p61: CAD file, 2020-04-29]
Ender-3 Mechanical/Ender-3 Upgrades/Direct Drive/_test/fits_hero_me/direct_drive_fits_e3d_v6_hero_me_M3x30.STL
59.6 x 32.8 x 43.5
