vincentkslim/Ender-3/Ender-3 Mechanical/Ender-3 Upgrades/E3D V6/e3d nozzle (0.2).SLDPRT

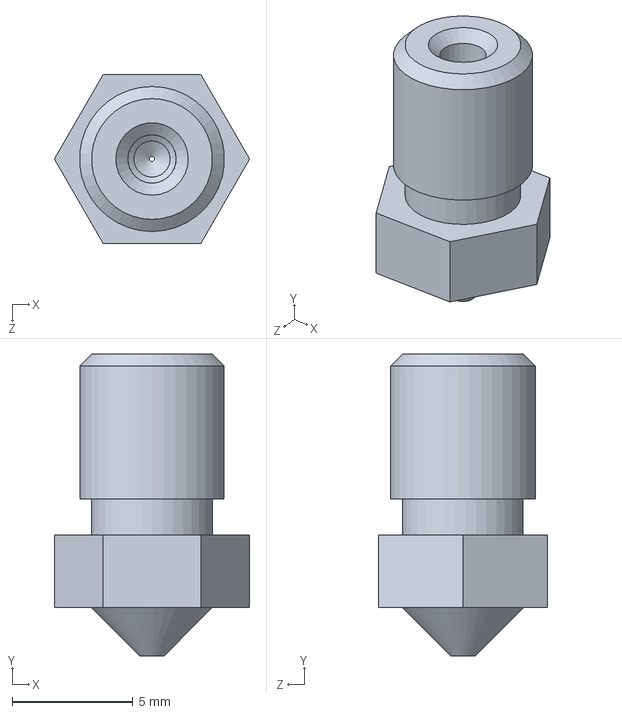
[picture p62: CAD file, 2020-04-29]
Ender-3 Mechanical/Ender-3 Upgrades/E3D V6/e3d nozzle (0.2).SLDPRT
8.08 x 12.5 x 7.00 mm
