vincentkslim/Ender-3/Ender-3 Mechanical/Ender-3 Upgrades/Radial Cooling Fan 50mm DC12V/turbine.SLDPRT

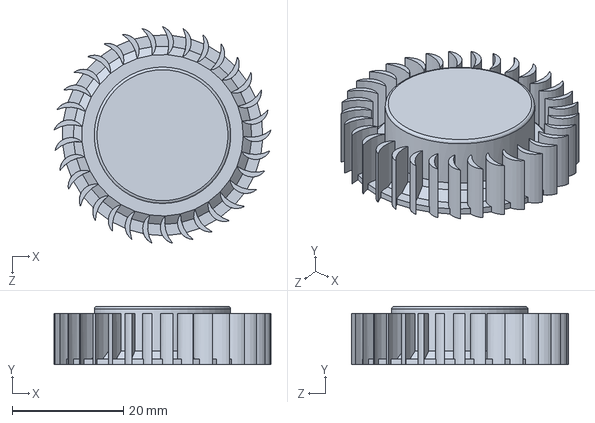
[picture p63: CAD file, 2020-07-11]
Ender-3 Mechanical/Ender-3 Upgrades/Radial Cooling Fan 50mm DC12V/turbine.SLDPRT
39.0 x 10.5 x 38.9 mm
