vincentkslim/Ender-3/Ender-3 Mechanical/Ender-3 Upgrades/Rear Electronics Case/_test/chain.SLDPRT

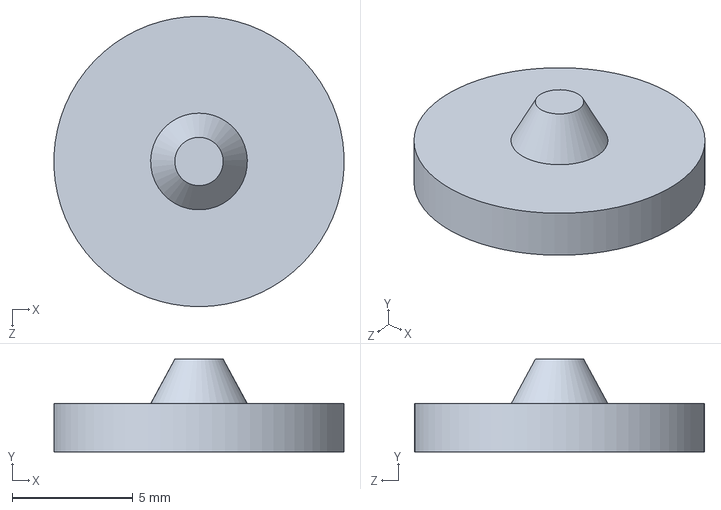
[picture p64: CAD file, 2020-04-09]
Ender-3 Mechanical/Ender-3 Upgrades/Rear Electronics Case/_test/chain.SLDPRT
12.0 x 3.84 x 12.0 mm
