vincentkslim/Ender-3/Ender-3 Mechanical/Ender-3 Upgrades/Rear Electronics Case/case_left.SLDPRT

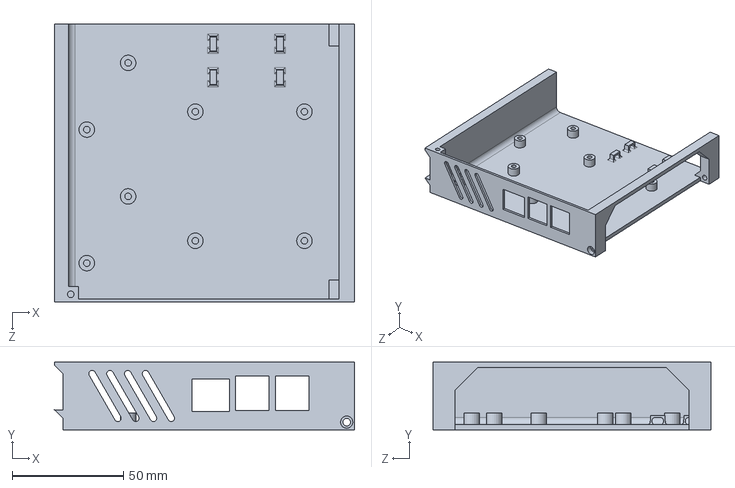
[picture p65: CAD file, 2020-12-05]
Ender-3 Mechanical/Ender-3 Upgrades/Rear Electronics Case/case_left.SLDPRT
134.8 x 30.5 x 125.0 mm
