vincentkslim/Ender-3/Ender-3 Mechanical/Ender-3 Parts/E gear.SLDPRT

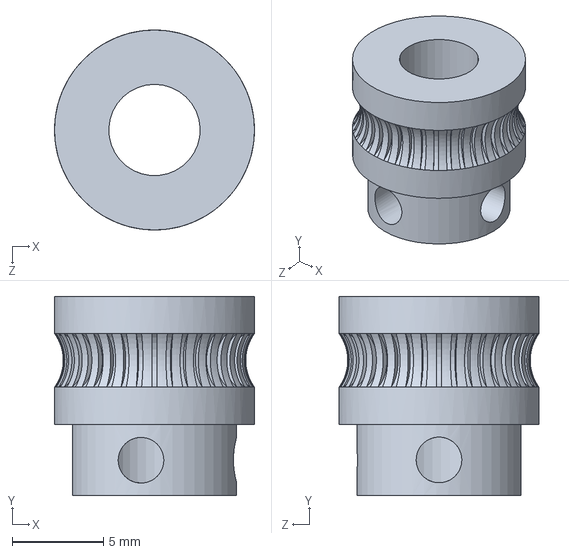
[picture p66: CAD file, 2020-12-05]
Ender-3 Mechanical/Ender-3 Parts/E gear.SLDPRT
11.0 x 10.9 x 10.9 mm
