vincentkslim/Ender-3/Ender-3 Mechanical/Ender-3 Upgrades/Rear Electronics Case/_stl/motherboad_hole_position.STL

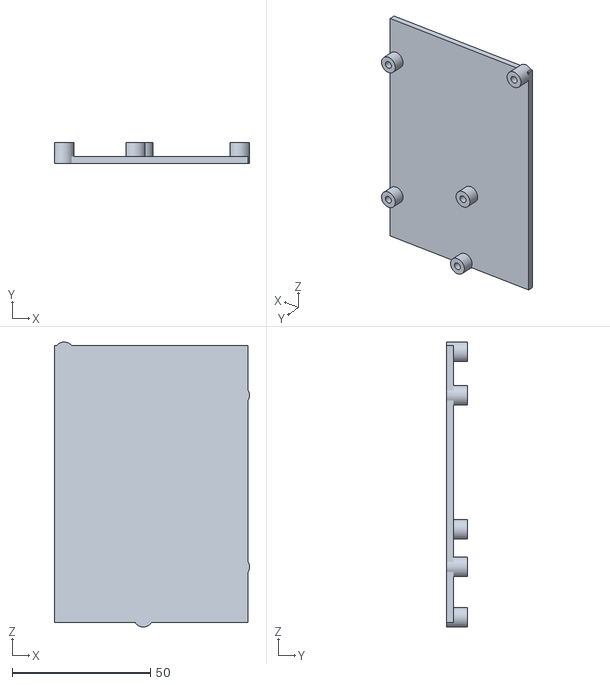
[picture p68: CAD file, 2020-04-09]
Ender-3 Mechanical/Ender-3 Upgrades/Rear Electronics Case/_stl/motherboad_hole_position.STL
70.5 x 7.50 x 103.0
