vincentkslim/Ender-3/Ender-3 Mechanical/Ender-3 Upgrades/Rear Electronics Case/lid_right.SLDPRT

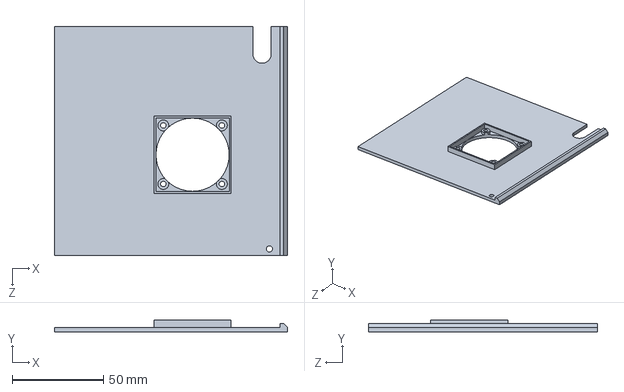
[picture p69: CAD file, 2020-07-11]
Ender-3 Mechanical/Ender-3 Upgrades/Rear Electronics Case/lid_right.SLDPRT
127.4 x 6.40 x 125.0 mm
