vincentkslim/Ender-3/Ender-3 Mechanical/Ender-3 Upgrades/X Carriage/002.SLDPRT

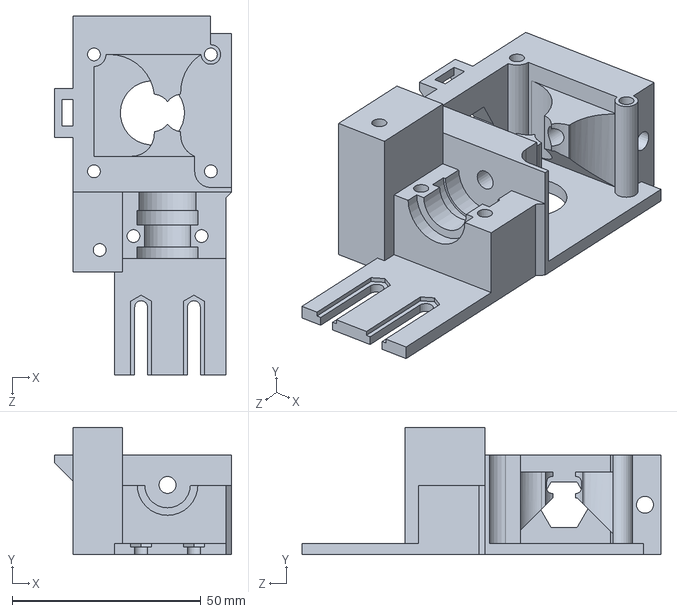
[picture p70: CAD file, 2020-12-05]
Ender-3 Mechanical/Ender-3 Upgrades/X Carriage/002.SLDPRT
47.0 x 33.8 x 95.2 mm
