vincentkslim/Ender-3/Ender-3 Mechanical/Ender-3 Parts/Extrusion Spring.SLDPRT

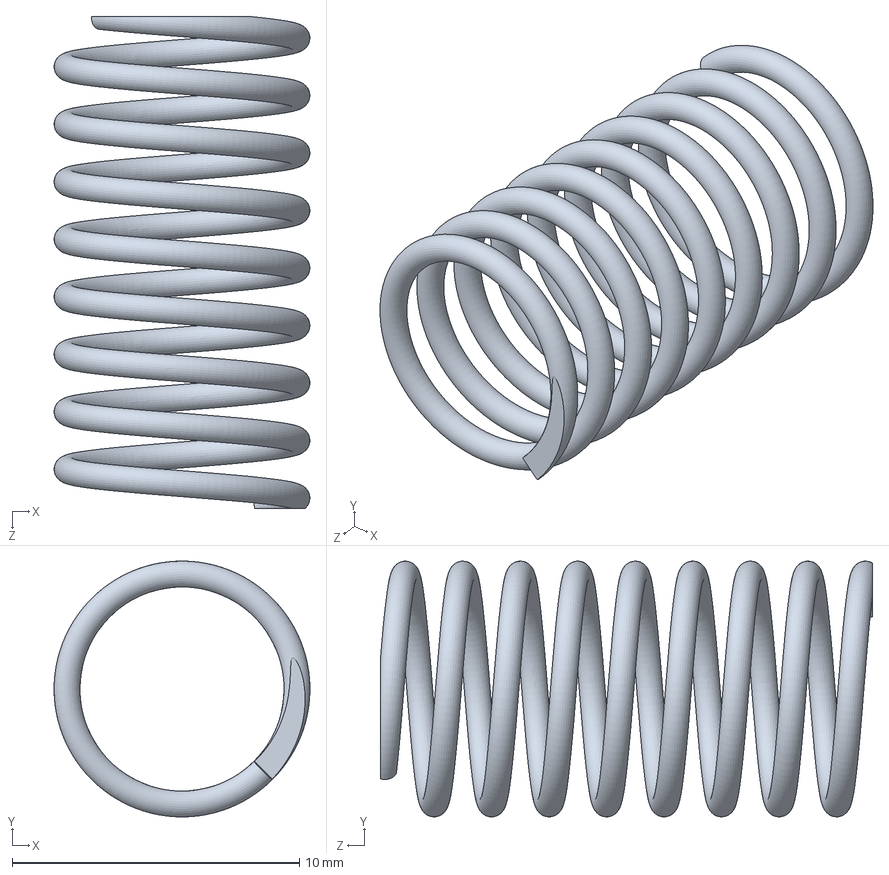
[picture p71: CAD file, 2020-12-05]
Ender-3 Mechanical/Ender-3 Parts/Extrusion Spring.SLDPRT
8.90 x 8.90 x 17.1 mm
