vincentkslim/Ender-3/Ender-3 Mechanical/Ender-3 Upgrades/Direct Drive/_test/fits_hero_me/Body4.sldprt

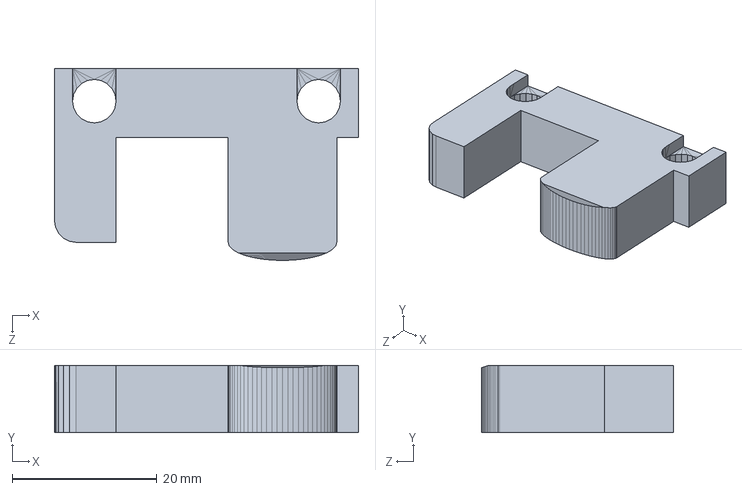
[picture p72: CAD file, 2020-04-29]
Ender-3 Mechanical/Ender-3 Upgrades/Direct Drive/_test/fits_hero_me/Body4.sldprt
42.0 x 9.30 x 26.5 mm
