vincentkslim/Ender-3/Ender-3 Mechanical/Ender-3 Upgrades/Rear Electronics Case/fan_cover.SLDPRT

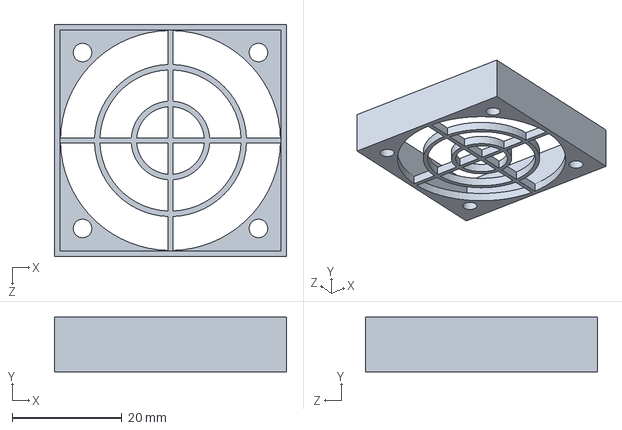
[picture p73: CAD file, 2020-07-11]
Ender-3 Mechanical/Ender-3 Upgrades/Rear Electronics Case/fan_cover.SLDPRT
42.2 x 10.0 x 42.2 mm
