vincentkslim/Ender-3/Ender-3 Mechanical/Ender-3 Upgrades/X Carriage/006.SLDPRT

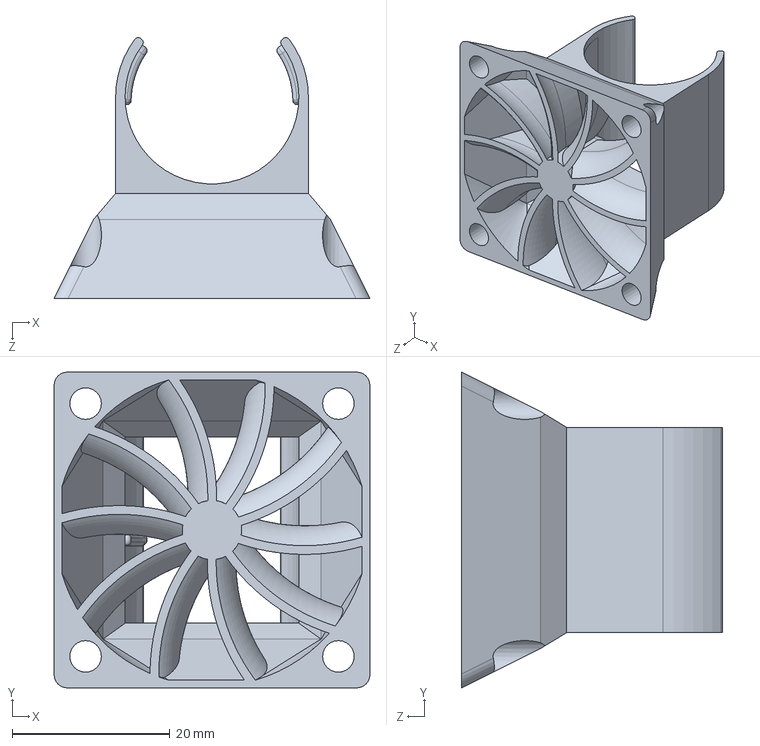
[picture p74: CAD file, 2020-12-05]
Ender-3 Mechanical/Ender-3 Upgrades/X Carriage/006.SLDPRT
40.0 x 40.0 x 33.0 mm
