vincentkslim/Ender-3/Ender-3 Mechanical/Ender-3 Parts/624U pillow.SLDPRT

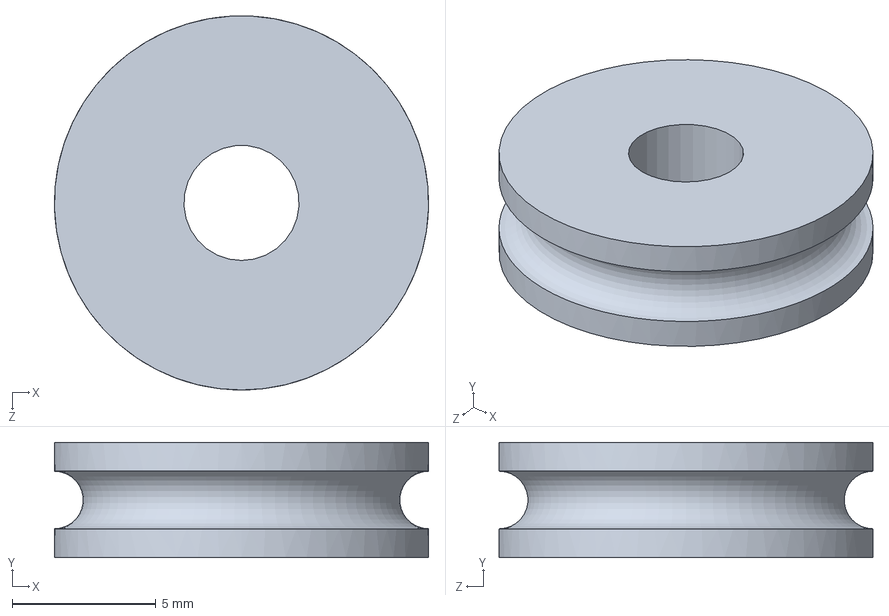
[picture p75: CAD file, 2020-12-05]
Ender-3 Mechanical/Ender-3 Parts/624U pillow.SLDPRT
13.0 x 4.00 x 13.0 mm
