vincentkslim/Ender-3/Ender-3 Mechanical/Ender-3 Upgrades/Rear Electronics Case/lid_left.SLDPRT

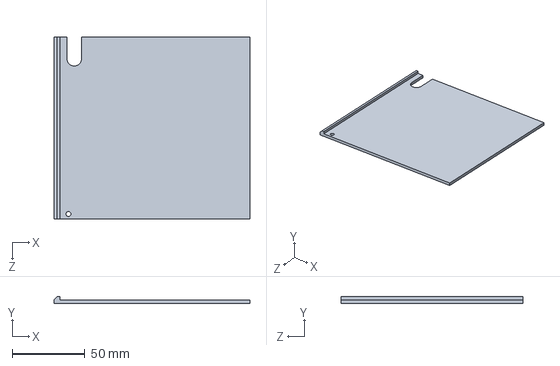
[picture p76: CAD file, 2020-07-11]
Ender-3 Mechanical/Ender-3 Upgrades/Rear Electronics Case/lid_left.SLDPRT
134.4 x 4.61 x 125.0 mm
