vincentkslim/Ender-3/Ender-3 Mechanical/Ender-3 Upgrades/X Carriage/004.SLDPRT

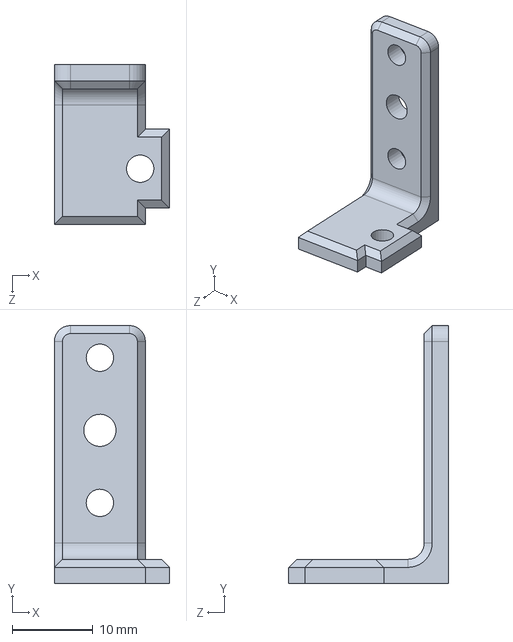
[picture p77: CAD file, 2020-12-05]
Ender-3 Mechanical/Ender-3 Upgrades/X Carriage/004.SLDPRT
14.3 x 32.0 x 19.8 mm
