vincentkslim/Ender-3/Ender-3 Mechanical/Ender-3 Parts/Y plate.SLDPRT

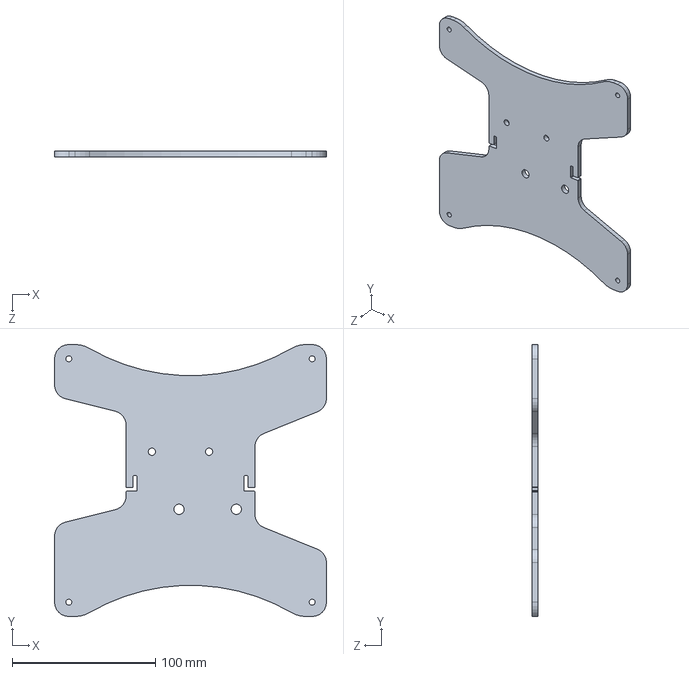
[picture p78: CAD file, 2020-07-11]
Ender-3 Mechanical/Ender-3 Parts/Y plate.SLDPRT
190.0 x 190.0 x 4.00 mm
