vincentkslim/Ender-3/Ender-3 Mechanical/Ender-3 Upgrades/E3D V6/fan sub2.SLDPRT

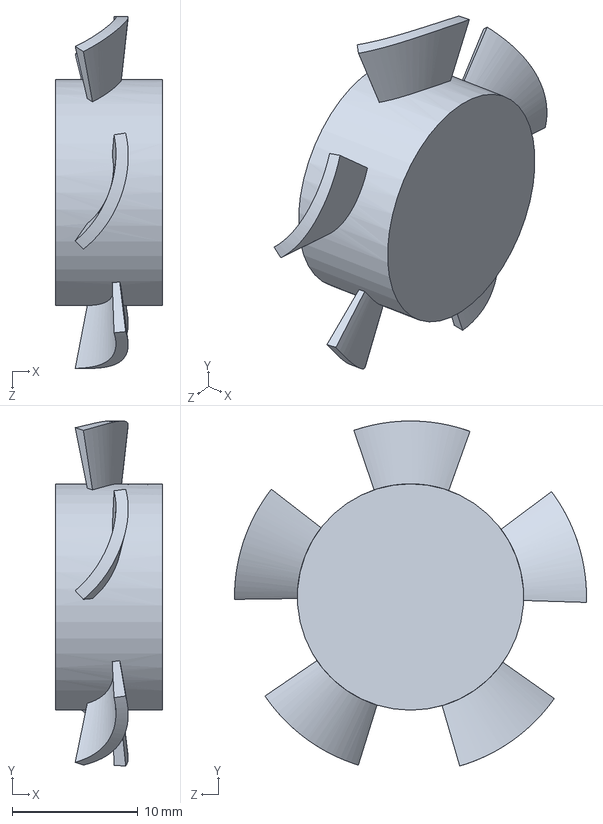
[picture p79: CAD file, 2020-04-29]
Ender-3 Mechanical/Ender-3 Upgrades/E3D V6/fan sub2.SLDPRT
8.50 x 27.4 x 28.0 mm
