vincentkslim/Ender-3/Ender-3 Mechanical/Ender-3 Upgrades/X Carriage/BL Touch.SLDPRT

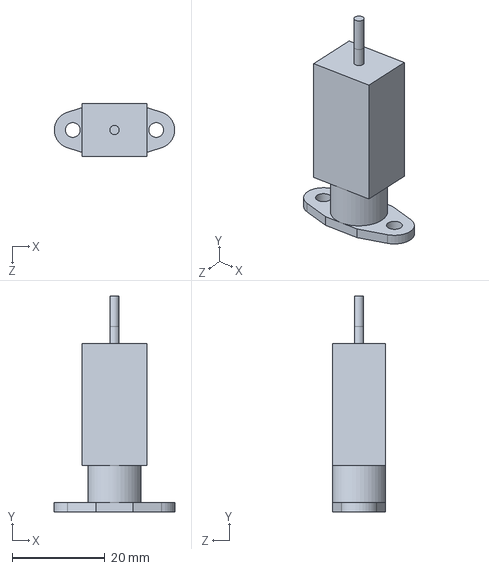
[picture p80: CAD file, 2020-12-05]
Ender-3 Mechanical/Ender-3 Upgrades/X Carriage/BL Touch.SLDPRT
26.0 x 46.6 x 11.5 mm
