vincentkslim/Ender-3/Ender-3 Mechanical/Ender-3 Parts/X Adjustment Block.SLDPRT

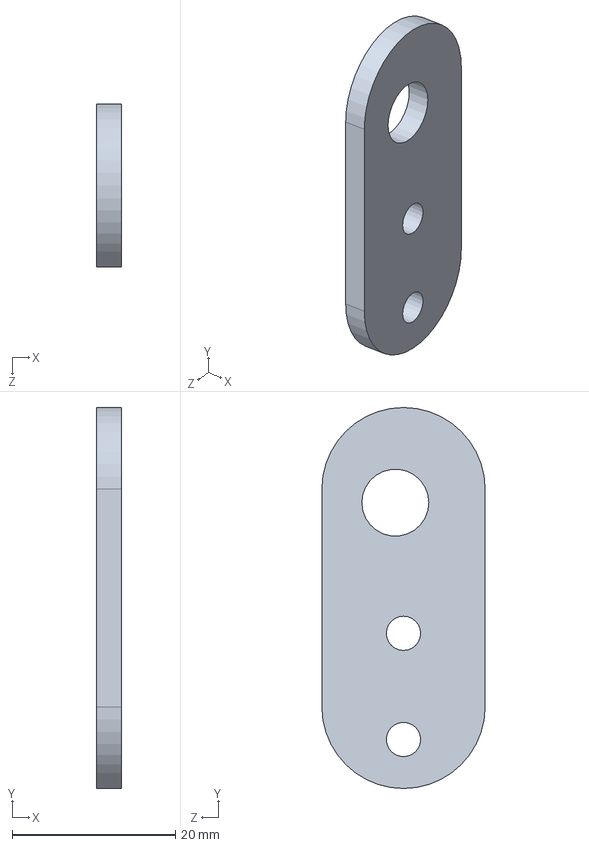
[picture p81: CAD file, 2020-07-11]
Ender-3 Mechanical/Ender-3 Parts/X Adjustment Block.SLDPRT
3.00 x 46.7 x 20.0 mm
