vincentkslim/Ender-3/Ender-3 Mechanical/Ender-3 Upgrades/E3D V6/fan sub1.SLDPRT

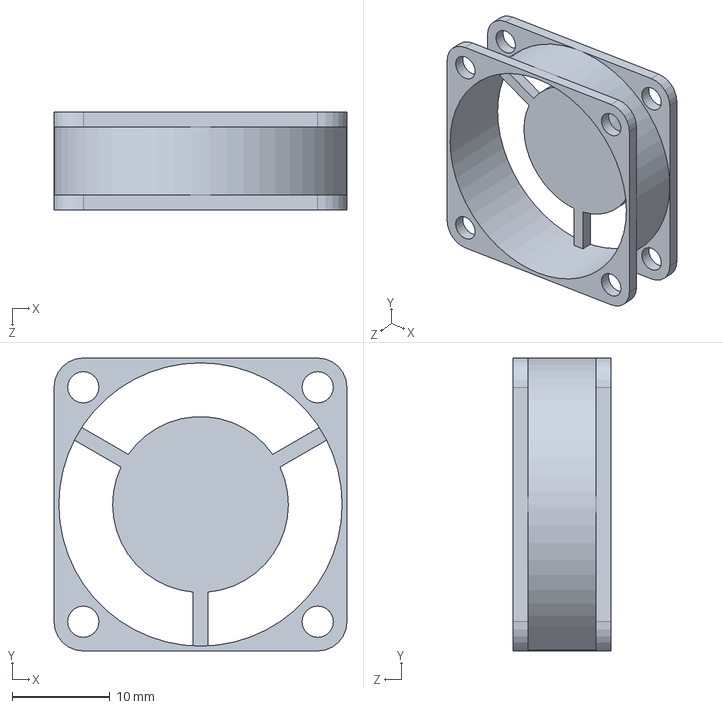
[picture p82: CAD file, 2020-04-29]
Ender-3 Mechanical/Ender-3 Upgrades/E3D V6/fan sub1.SLDPRT
30.0 x 30.0 x 10.0 mm
