vincentkslim/Ender-3/Ender-3 Mechanical/Ender-3 Upgrades/X Carriage/fan-duct.SLDPRT

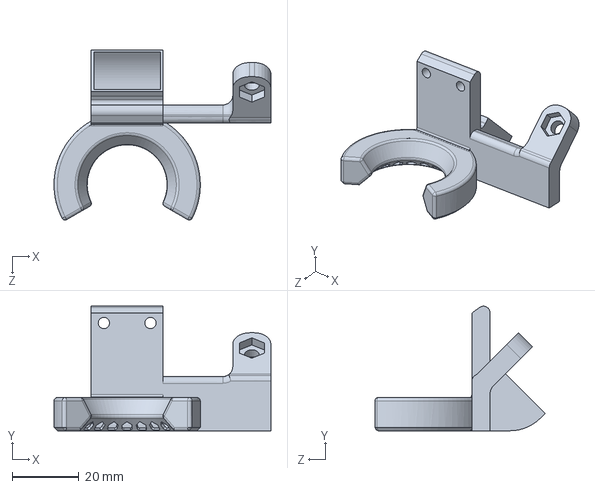
[picture p83: CAD file, 2020-12-05]
Ender-3 Mechanical/Ender-3 Upgrades/X Carriage/fan-duct.SLDPRT
65.2 x 37.5 x 51.1 mm
