vincentkslim/Ender-3/Ender-3 Mechanical/Ender-3 Parts/lcd.SLDPRT

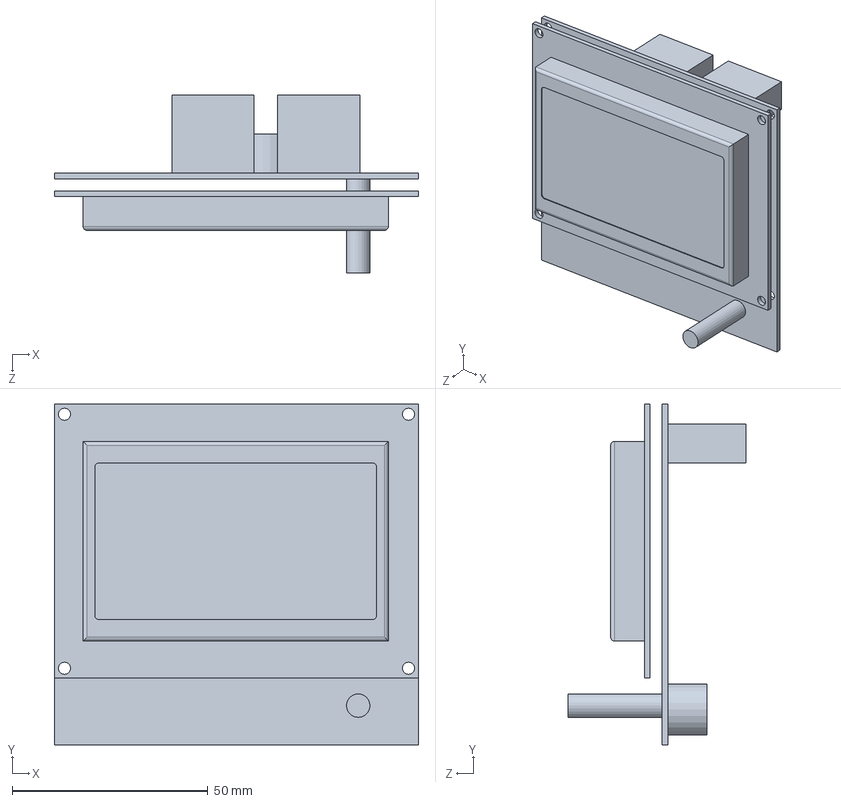
[picture p84: CAD file, 2020-07-11]
Ender-3 Mechanical/Ender-3 Parts/lcd.SLDPRT
93.0 x 87.0 x 45.5 mm
