vincentkslim/Ender-3/Ender-3 Mechanical/Ender-3 Parts/2040-3R profile.SLDPRT

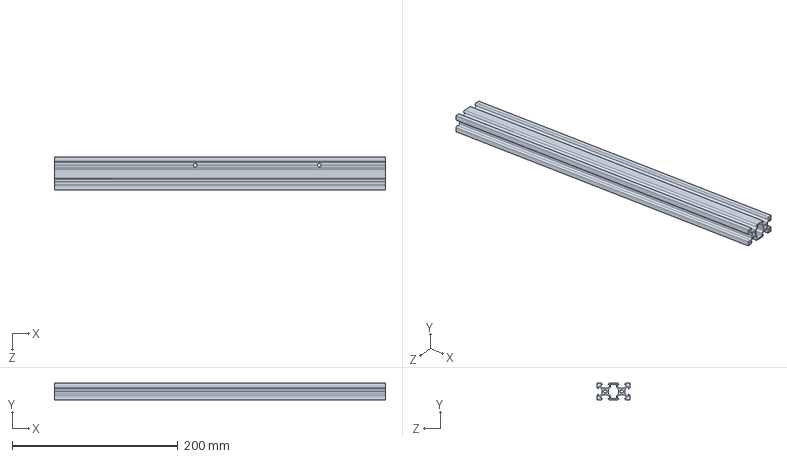
[picture p85: CAD file, 2020-07-11]
Ender-3 Mechanical/Ender-3 Parts/2040-3R profile.SLDPRT
400.0 x 20.0 x 40.0 mm
