vincentkslim/Ender-3/Ender-3 Mechanical/Ender-3 Upgrades/E3D V6/e3d heat break.SLDPRT

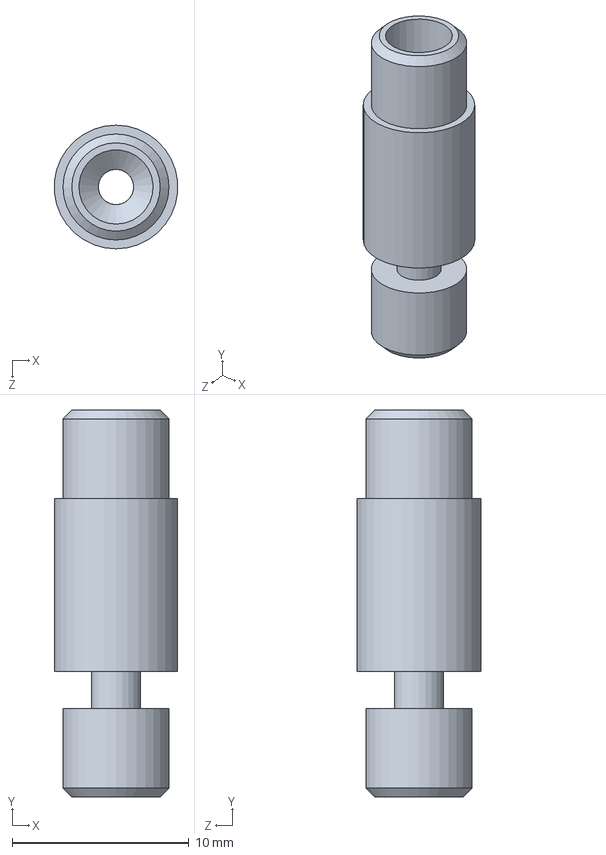
[picture p86: CAD file, 2020-04-29]
Ender-3 Mechanical/Ender-3 Upgrades/E3D V6/e3d heat break.SLDPRT
6.97 x 21.9 x 7.00 mm
