vincentkslim/Ender-3/Ender-3 Mechanical/Ender-3 Upgrades/X Carriage/40mm Duct.SLDPRT

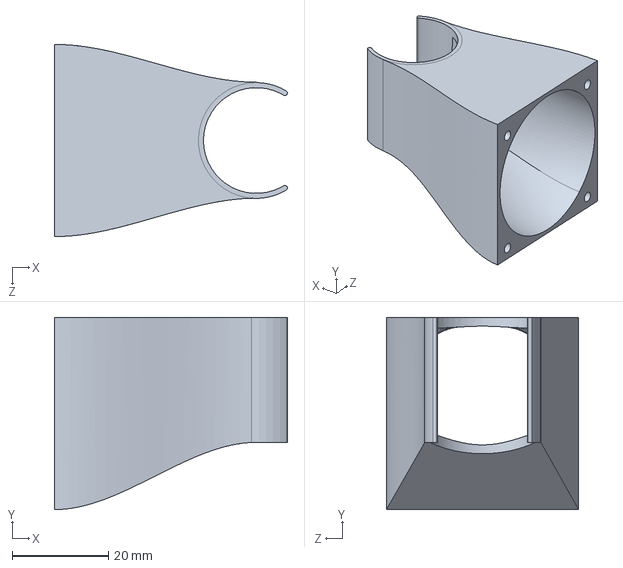
[picture p87: CAD file, 2020-12-05]
Ender-3 Mechanical/Ender-3 Upgrades/X Carriage/40mm Duct.SLDPRT
48.5 x 40.0 x 40.0 mm
