vincentkslim/Ender-3/Ender-3 Mechanical/Ender-3 Parts/X motor bracket.SLDPRT

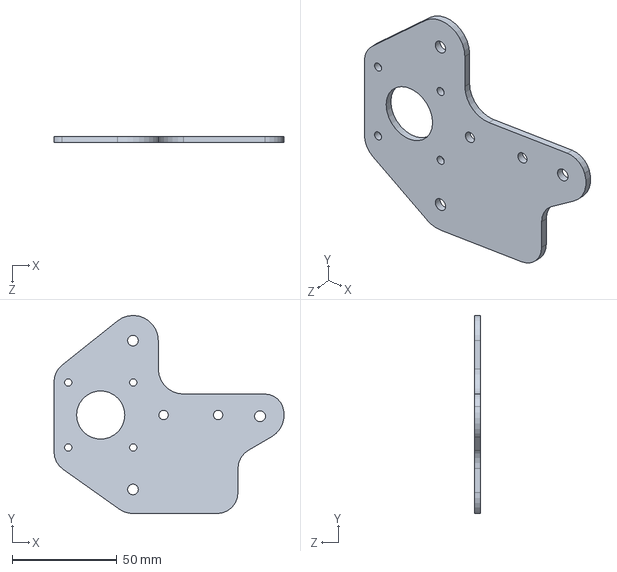
[picture p88: CAD file, 2020-07-11]
Ender-3 Mechanical/Ender-3 Parts/X motor bracket.SLDPRT
109.7 x 94.5 x 3.00 mm
