vincentkslim/Ender-3/Ender-3 Mechanical/Ender-3 Upgrades/E3D V6/e3d heatsink.SLDPRT

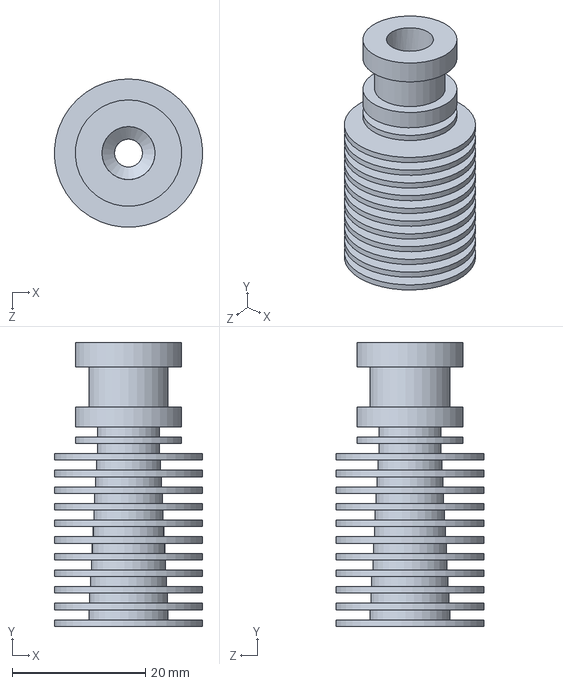
[picture p89: CAD file, 2020-04-29]
Ender-3 Mechanical/Ender-3 Upgrades/E3D V6/e3d heatsink.SLDPRT
22.3 x 42.7 x 22.3 mm
