vincentkslim/Ender-3/Ender-3 Mechanical/Ender-3 Upgrades/X Carriage/4020 fan.SLDPRT

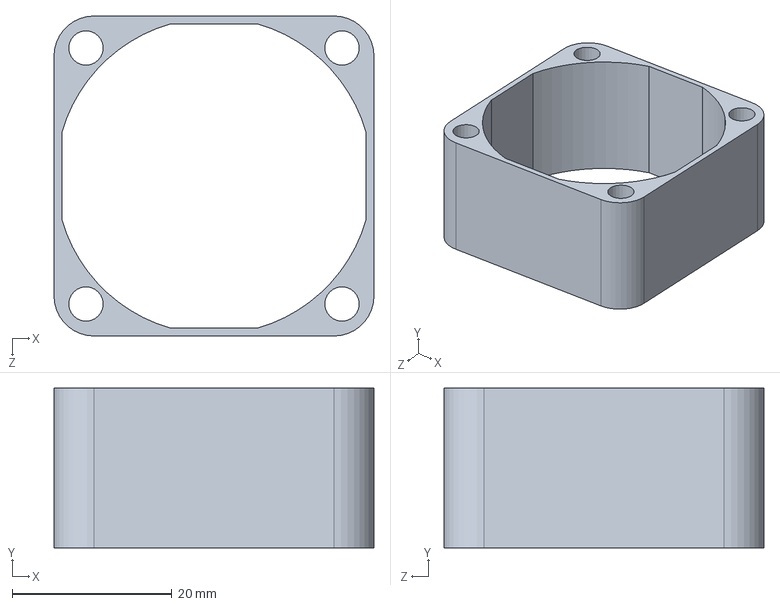
[picture p90: CAD file, 2020-12-05]
Ender-3 Mechanical/Ender-3 Upgrades/X Carriage/4020 fan.SLDPRT
40.0 x 20.0 x 40.0 mm
