vincentkslim/Ender-3/Ender-3 Mechanical/Ender-3 Upgrades/E3D V6/e3d heaterblock.SLDPRT

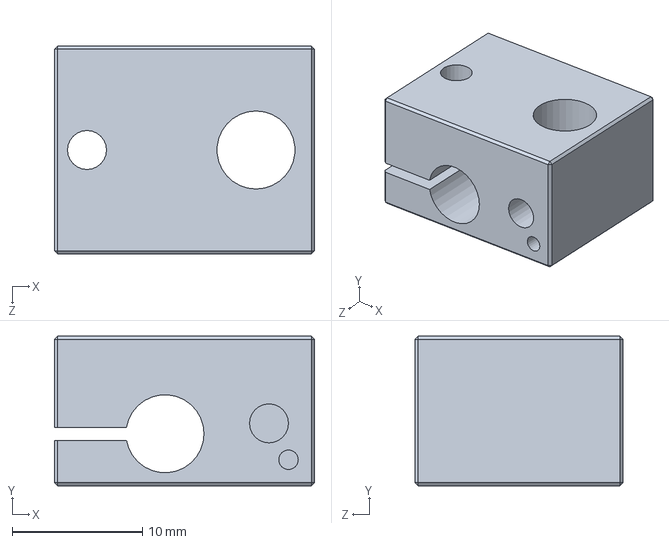
[picture p91: CAD file, 2020-04-29]
Ender-3 Mechanical/Ender-3 Upgrades/E3D V6/e3d heaterblock.SLDPRT
20.0 x 11.5 x 16.0 mm
