vincentkslim/Ender-3/Ender-3 Mechanical/Ender-3 Upgrades/X Carriage/001.SLDPRT

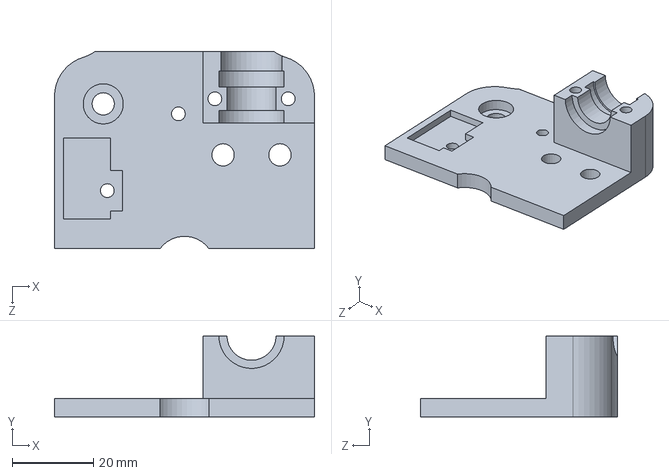
[picture p92: CAD file, 2020-12-05]
Ender-3 Mechanical/Ender-3 Upgrades/X Carriage/001.SLDPRT
64.0 x 19.9 x 48.5 mm
