vincentkslim/Ender-3/Ender-3 Mechanical/Ender-3 Upgrades/X Carriage/M10 thread test.SLDPRT

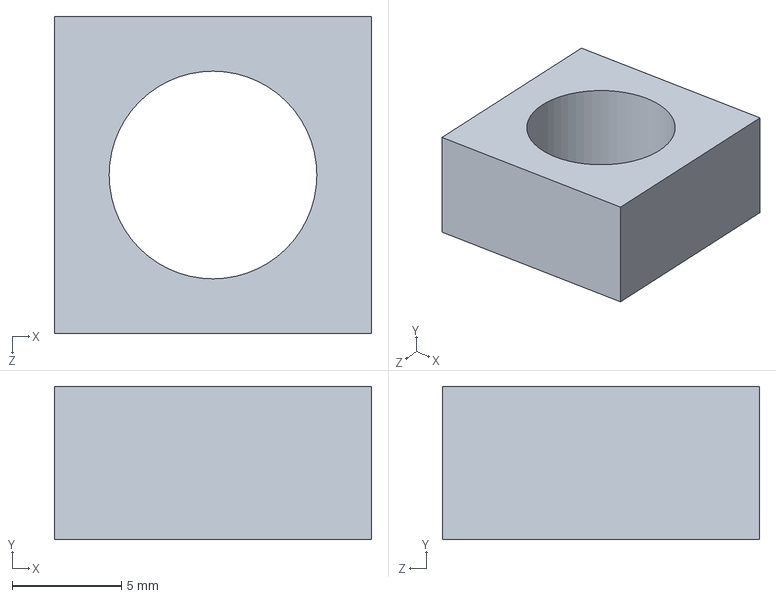
[picture p93: CAD file, 2020-12-05]
Ender-3 Mechanical/Ender-3 Upgrades/X Carriage/M10 thread test.SLDPRT
14.5 x 7.00 x 14.5 mm
