vincentkslim/Ender-3/Ender-3 Mechanical/Ender-3 Upgrades/X Carriage/bondtech_drivegear_needle_bearing.sldprt

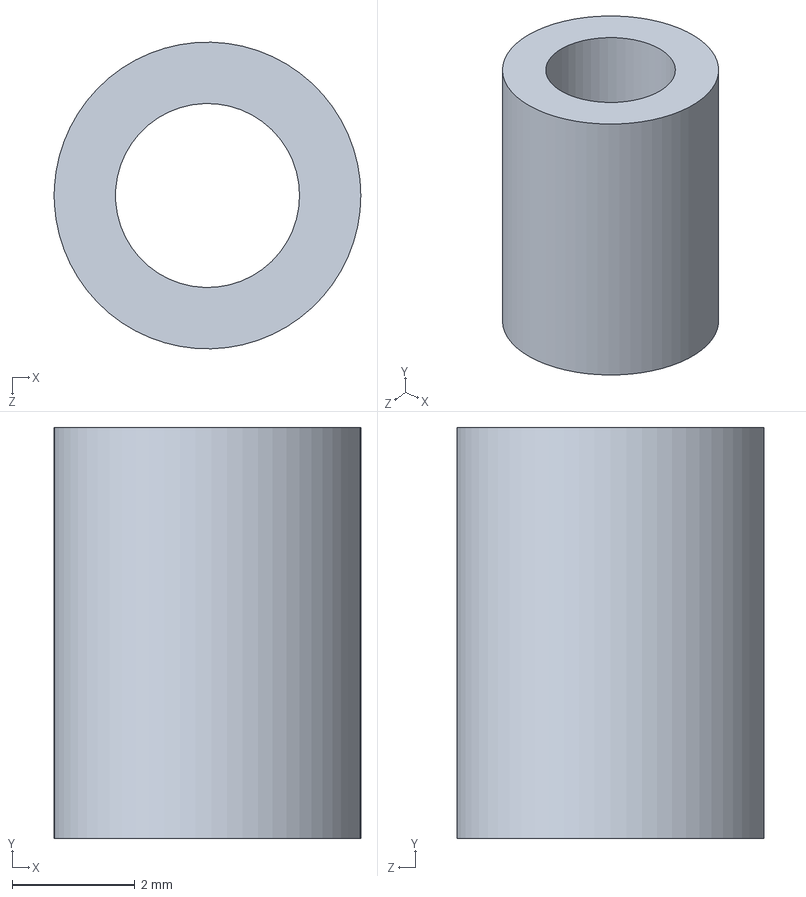
[picture p94: CAD file, 2020-04-29]
Ender-3 Mechanical/Ender-3 Upgrades/X Carriage/bondtech_drivegear_needle_bearing.sldprt
5.00 x 6.70 x 5.00 mm
