vincentkslim/Ender-3/Ender-3 Mechanical/Ender-3 Upgrades/X Carriage/bondtech_drivegear_idler.sldprt

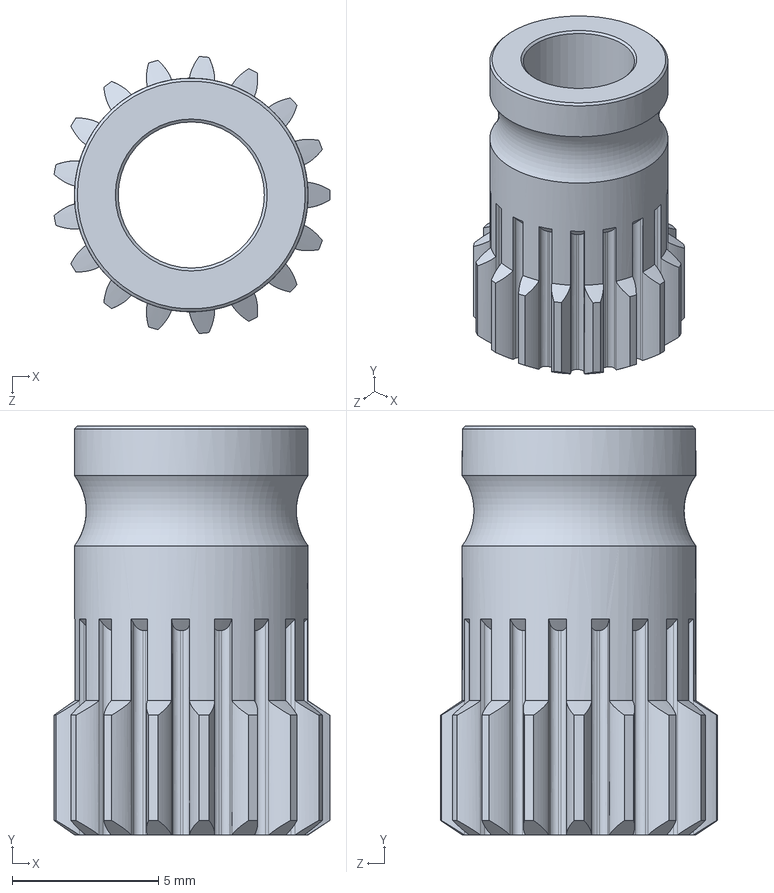
[picture p95: CAD file, 2020-04-29]
Ender-3 Mechanical/Ender-3 Upgrades/X Carriage/bondtech_drivegear_idler.sldprt
9.44 x 14.0 x 9.48 mm
