vincentkslim/Ender-3/Ender-3 Mechanical/Ender-3 Parts/E motor bracket.SLDPRT

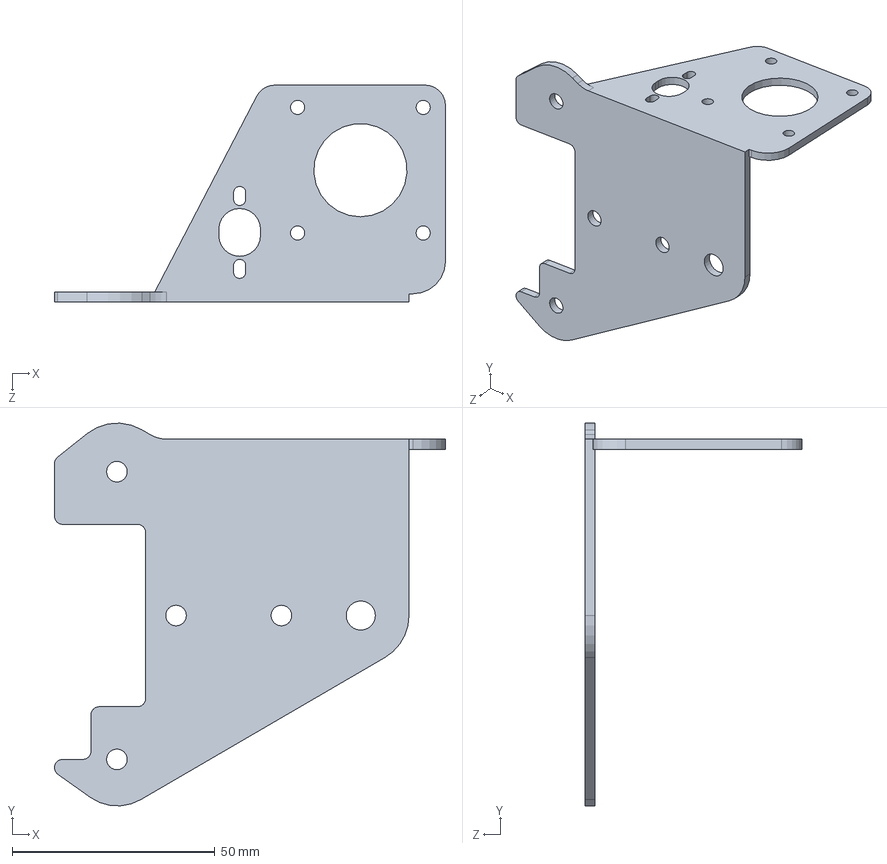
[picture p96: CAD file, 2020-07-11]
Ender-3 Mechanical/Ender-3 Parts/E motor bracket.SLDPRT
96.5 x 94.5 x 53.5 mm
