vincentkslim/Ender-3/Ender-3 Mechanical/Ender-3 Upgrades/X Carriage/bondtech_drivegear_shaft.sldprt

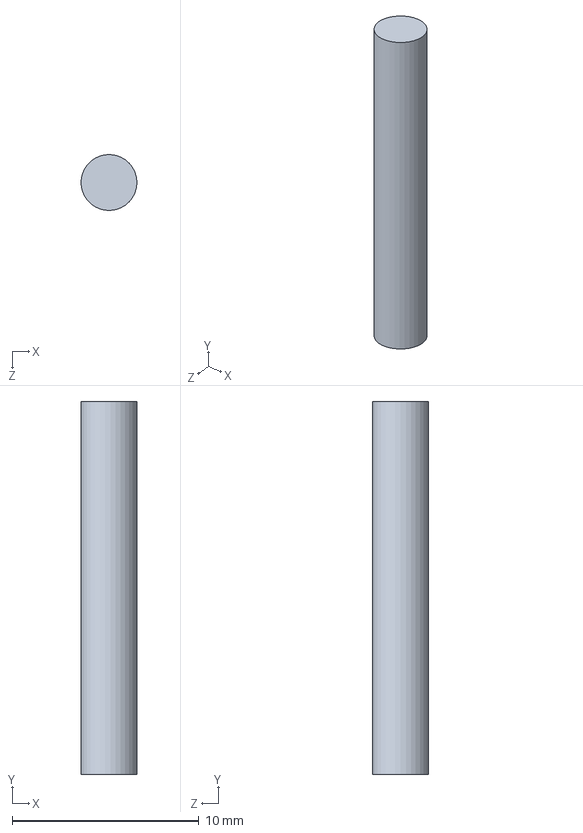
[picture p97: CAD file, 2020-04-29]
Ender-3 Mechanical/Ender-3 Upgrades/X Carriage/bondtech_drivegear_shaft.sldprt
3.00 x 20.0 x 3.00 mm
