vincentkslim/Ender-3/Ender-3 Mechanical/Ender-3 Parts/2GT-pulley.SLDPRT

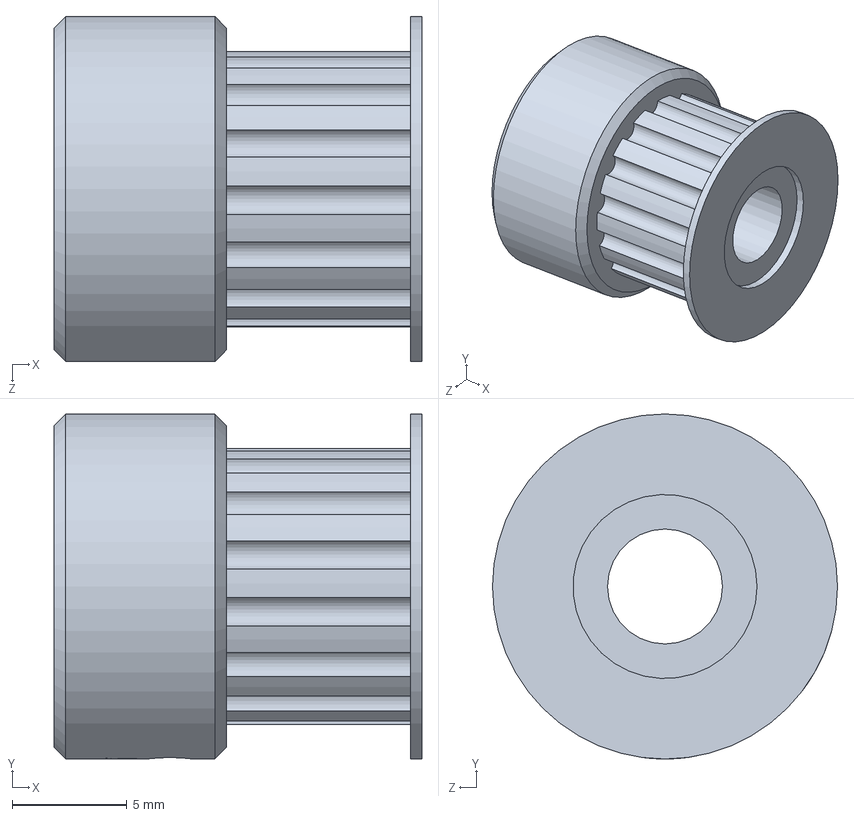
[picture p98: CAD file, 2020-07-11]
Ender-3 Mechanical/Ender-3 Parts/2GT-pulley.SLDPRT
16.0 x 15.0 x 15.0 mm
