vincentkslim/Ender-3/Ender-3 Mechanical/Ender-3 Parts/Y belt.SLDPRT

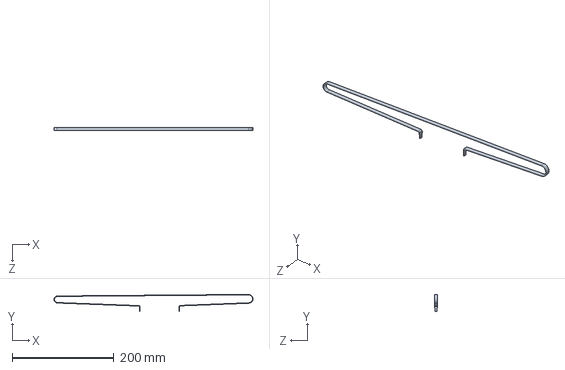
[picture p100: CAD file, 2020-07-11]
Ender-3 Mechanical/Ender-3 Parts/Y belt.SLDPRT
391.8 x 33.8 x 6.00 mm
