vincentkslim/Ender-3/Ender-3 Mechanical/Ender-3 Parts/Y Adjustment Block.SLDPRT

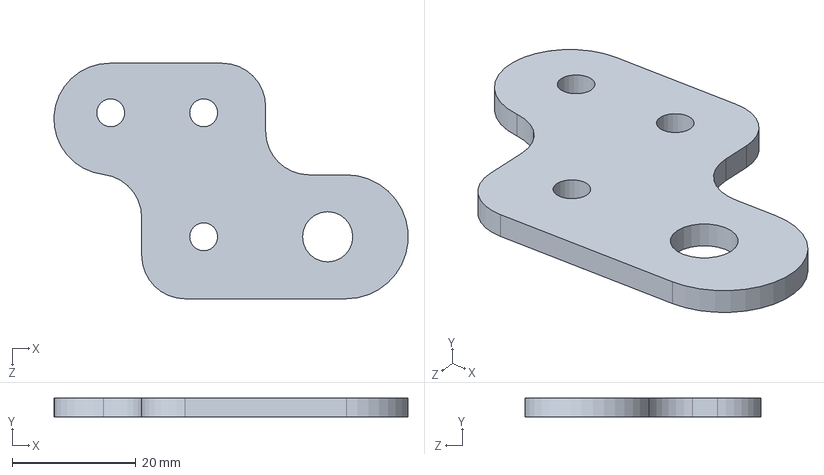
[picture p101: CAD file, 2020-07-11]
Ender-3 Mechanical/Ender-3 Parts/Y Adjustment Block.SLDPRT
57.1 x 3.00 x 38.0 mm
