vincentkslim/Ender-3/Ender-3 Mechanical/Ender-3 Parts/Z motor bracket.SLDPRT

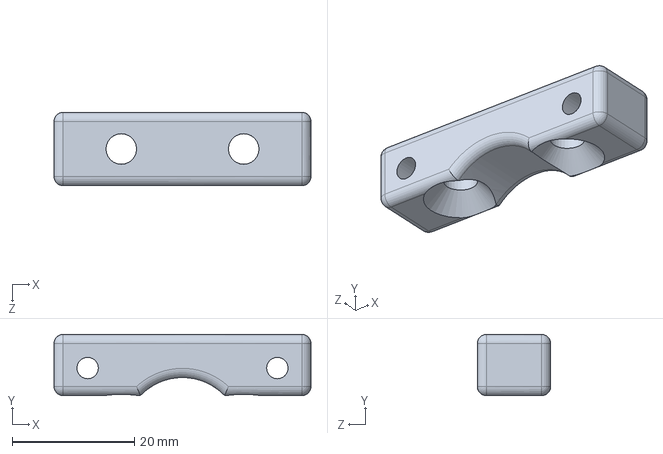
[picture p102: CAD file, 2020-07-11]
Ender-3 Mechanical/Ender-3 Parts/Z motor bracket.SLDPRT
42.0 x 10.0 x 12.0 mm
