vincentkslim/Ender-3/Ender-3 Mechanical/Ender-3 Parts/Hot bed.SLDPRT

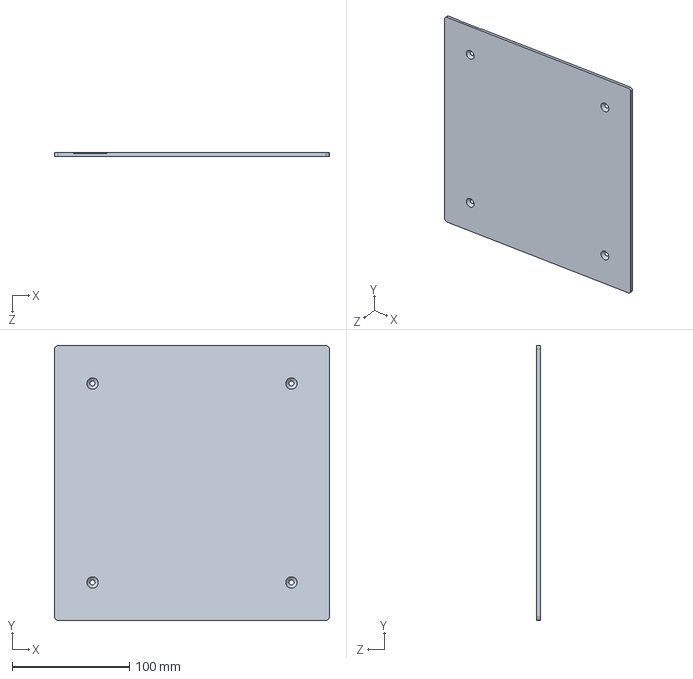
[picture p103: CAD file, 2020-07-11]
Ender-3 Mechanical/Ender-3 Parts/Hot bed.SLDPRT
235.0 x 235.0 x 3.00 mm
