vincentkslim/Ender-3/Ender-3 Mechanical/Ender-3 Parts/Z coupler.SLDPRT

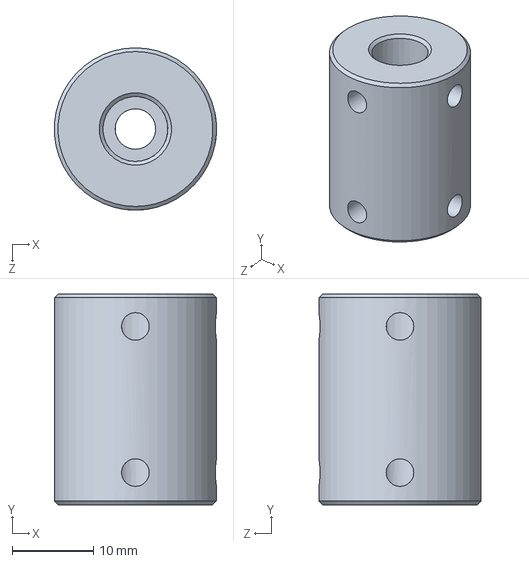
[picture p104: CAD file, 2020-07-11]
Ender-3 Mechanical/Ender-3 Parts/Z coupler.SLDPRT
20.0 x 26.0 x 20.0 mm
