vincentkslim/Ender-3/Ender-3 Mechanical/Ender-3 Upgrades/raspberry-pi-3-model-b-reference-design-solidworks-cad-rpi-raspberrypi-raspberry-pi-1.snapshot.83/Solidworks Complete Assembly/Rpi components/raspberry_pi_B+_(microsd2).SLDPRT

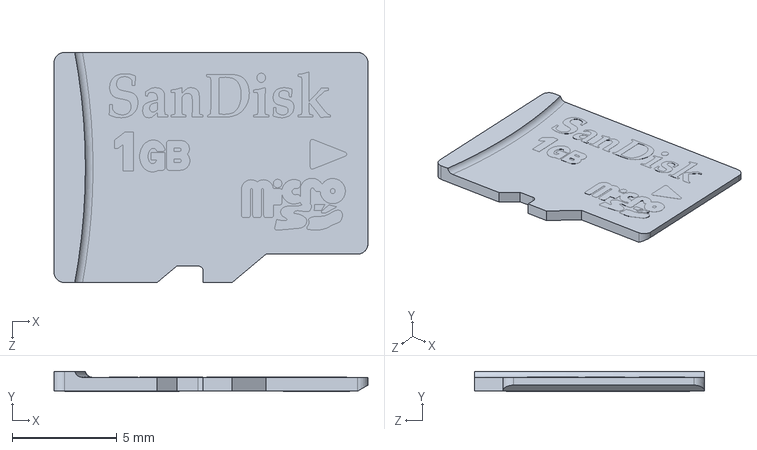
[picture p105: CAD file, 2020-07-11]
Ender-3 Mechanical/Ender-3 Upgrades/raspberry-pi-3-model-b-reference-design-solidworks-cad-rpi-raspberrypi-raspberry-pi-1.snapshot.83/Solidworks Complete Assembly/Rpi components/raspberry_pi_B+_(micr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
15.0 x 0.975 x 11.0 mm
